JerzySukiennik/gzowo-glass/renders/glass-scan-side.png

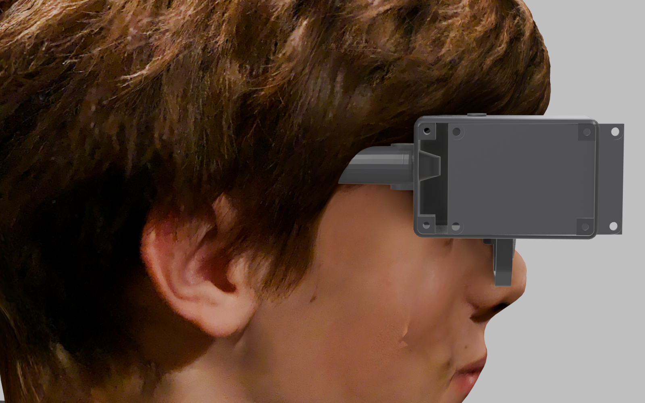
renders/glass-scan-side.png
