JerzySukiennik/gzowo-glass/renders/glass-scan-top-xray.png

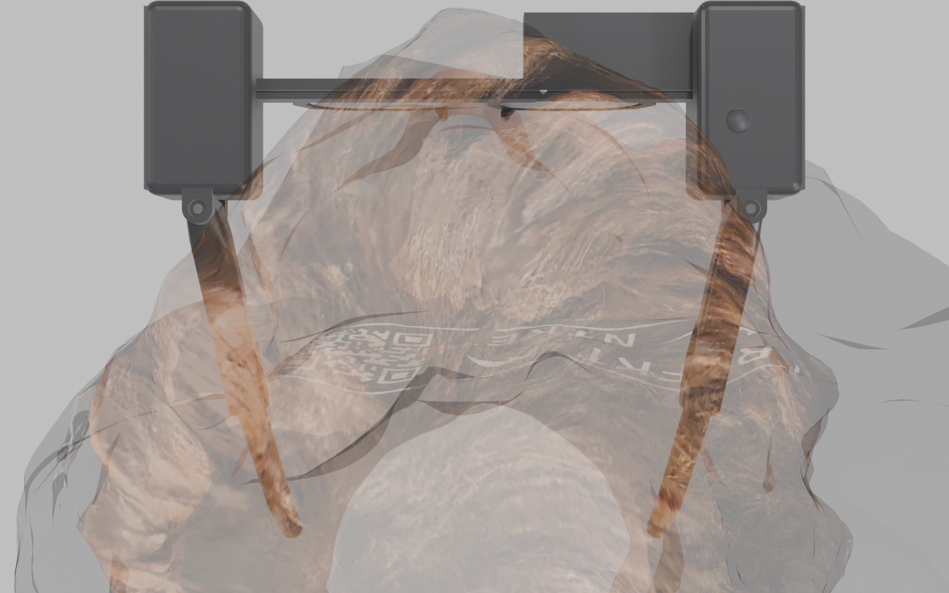
renders/glass-scan-top-xray.png
