JerzySukiennik/gzowo-glass/docs/glass/assets/v0.6/exploded.png

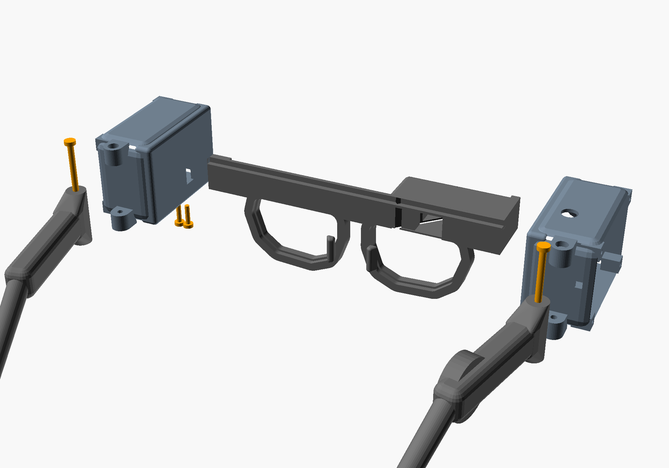
docs/glass/assets/v0.6/exploded.png
