JerzySukiennik/gzowo-glass/docs/glass/assets/v0.6/eye.webp

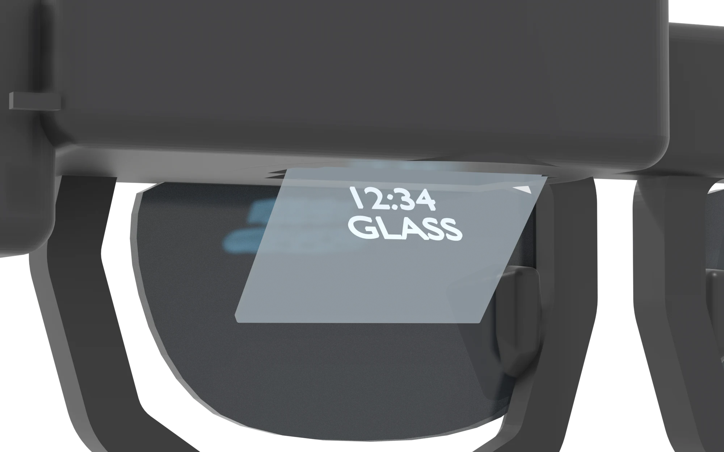
docs/glass/assets/v0.6/eye.webp
