JerzySukiennik/gzowo-glass/docs/glass/assets/v0.6/frames/f036.webp

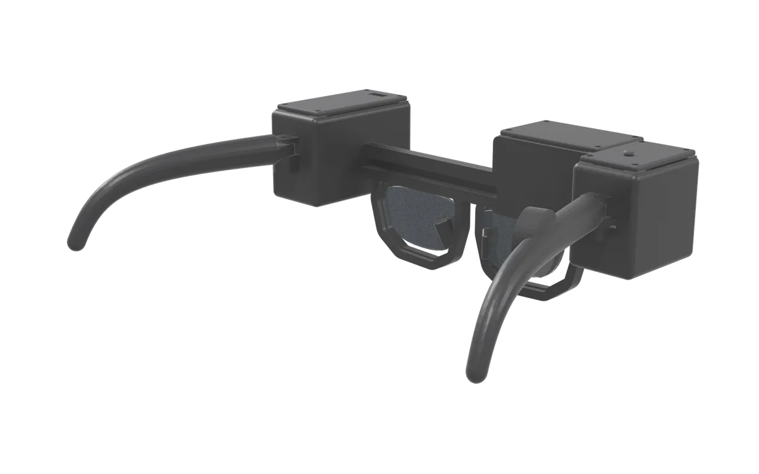
docs/glass/assets/v0.6/frames/f036.webp
