JerzySukiennik/gzowo-glass/docs/glass/assets/v0.6/frames/f054.webp

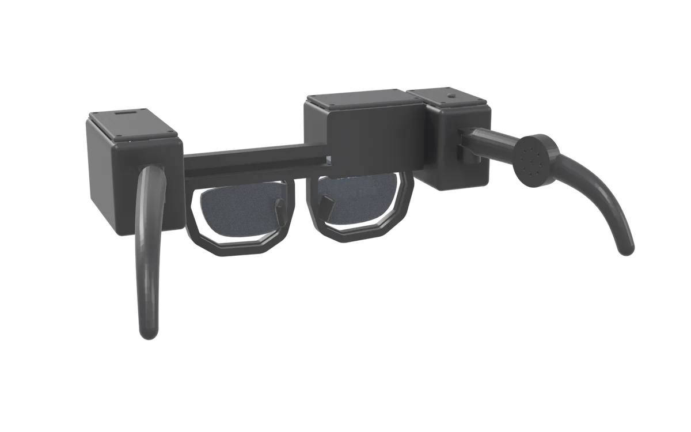
docs/glass/assets/v0.6/frames/f054.webp
