JerzySukiennik/gzowo-glass/docs/glass/assets/v0.6/frames/f074.webp

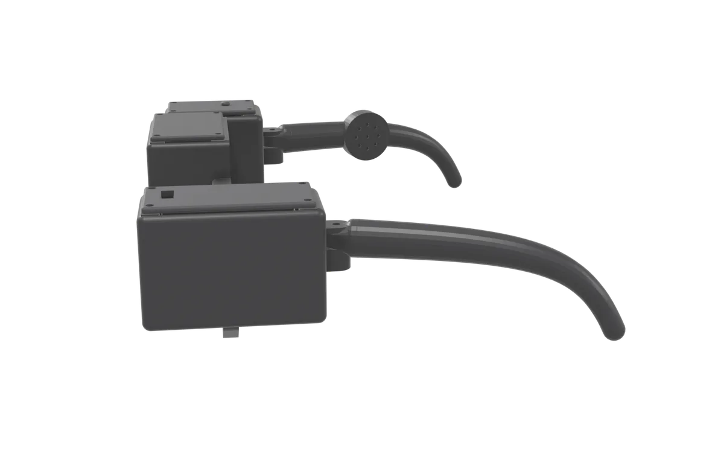
docs/glass/assets/v0.6/frames/f074.webp
