JerzySukiennik/gzowo-glass/docs/glass/assets/v0.6/frames/f085.webp

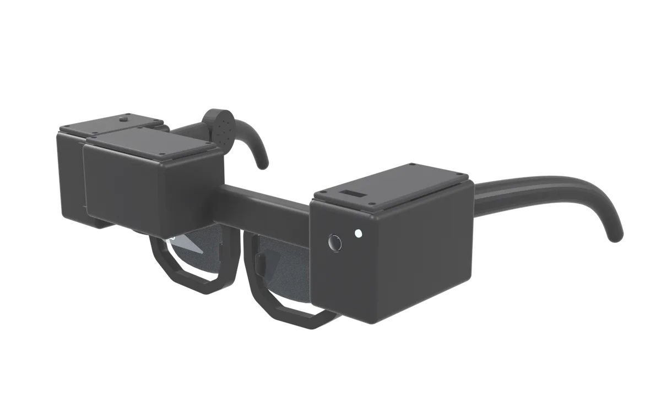
docs/glass/assets/v0.6/frames/f085.webp
