JerzySukiennik/gzowo-glass/docs/glass/assets/v0.6/front.webp

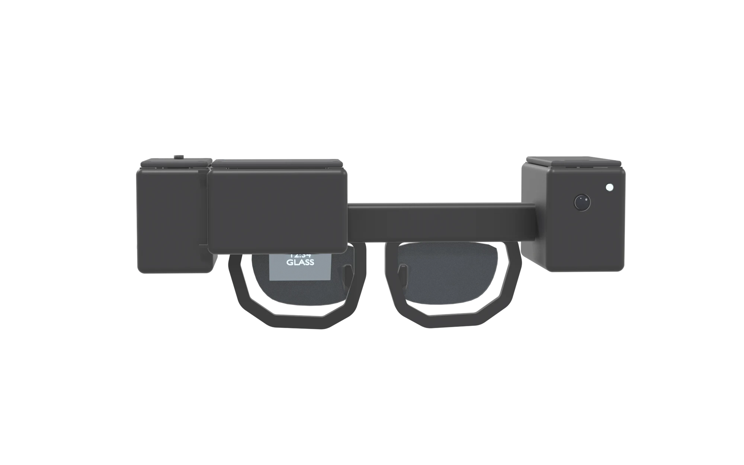
docs/glass/assets/v0.6/front.webp
