JerzySukiennik/gzowo-glass/docs/glass/assets/v0.6/head.webp

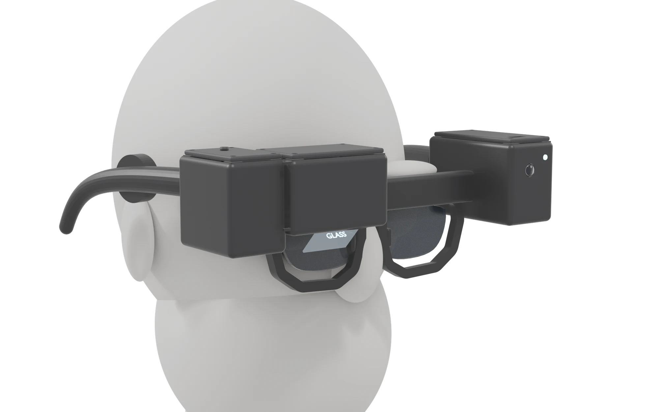
docs/glass/assets/v0.6/head.webp
