JerzySukiennik/gzowo-glass/docs/glass/assets/v0.6/hero.webp

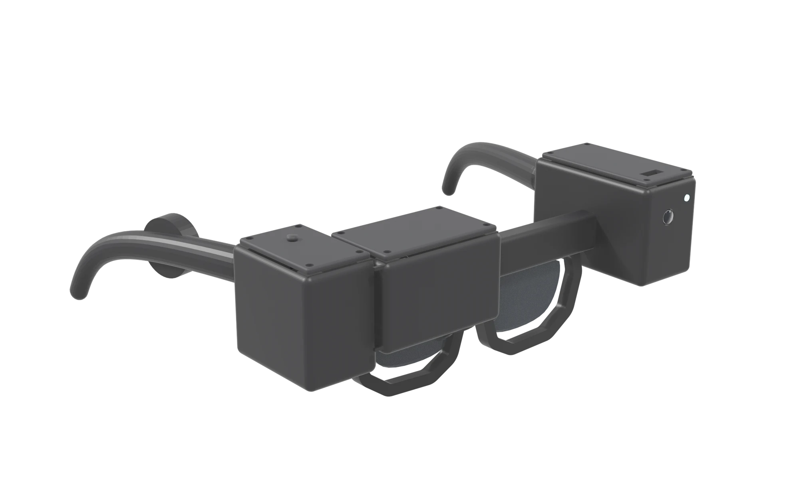
docs/glass/assets/v0.6/hero.webp
