JerzySukiennik/gzowo-glass/docs/glass/assets/v0.6/left.webp

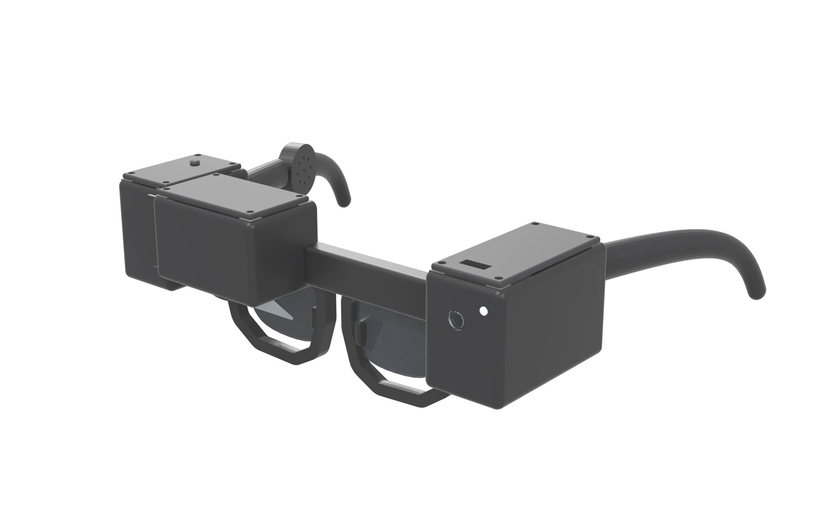
docs/glass/assets/v0.6/left.webp
