JerzySukiennik/gzowo-glass/docs/glass/assets/v0.6/pod.webp

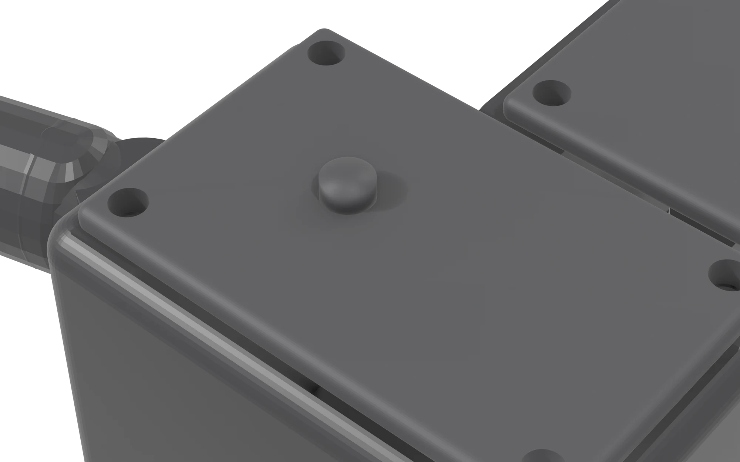
docs/glass/assets/v0.6/pod.webp
