JerzySukiennik/gzowo-glass/docs/smendilendi/assets/v0.5/detail.webp

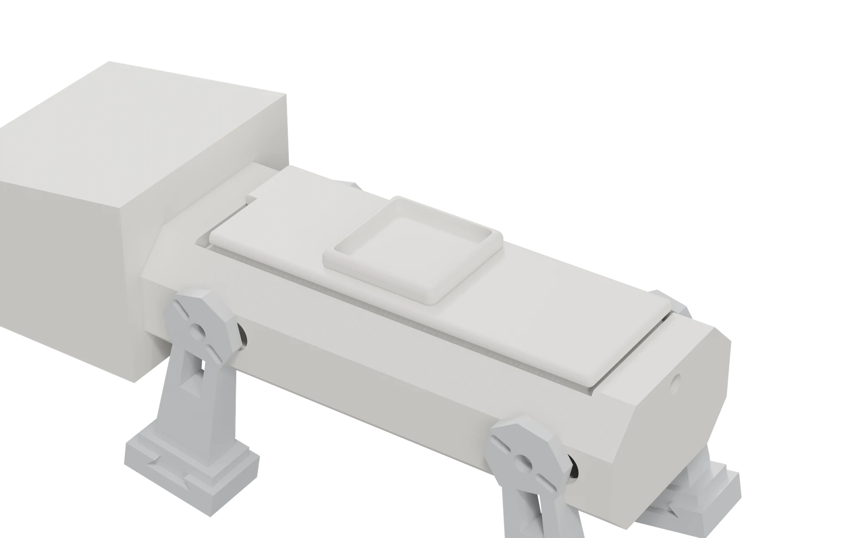
docs/smendilendi/assets/v0.5/detail.webp
