JerzySukiennik/gzowo-glass/docs/smendilendi/assets/v0.5/frames/f015.webp

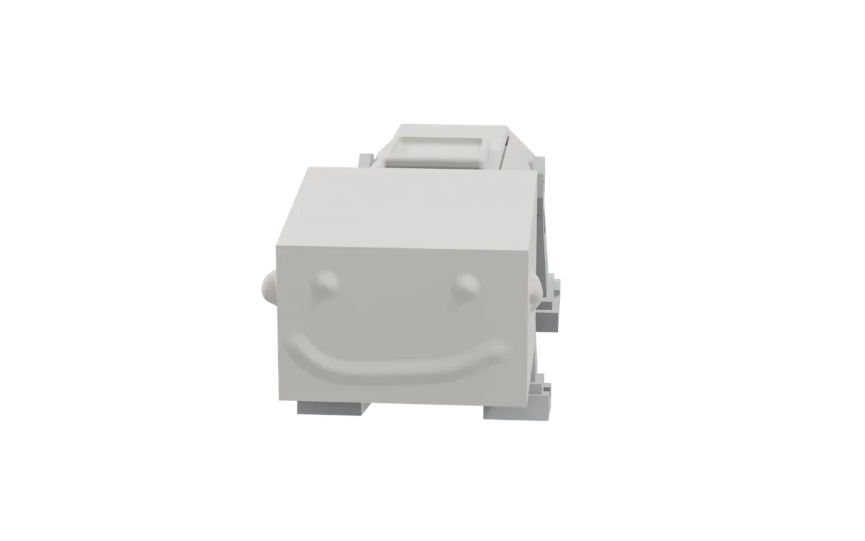
docs/smendilendi/assets/v0.5/frames/f015.webp
