JerzySukiennik/gzowo-glass/docs/smendilendi/assets/v0.5/frames/f086.webp

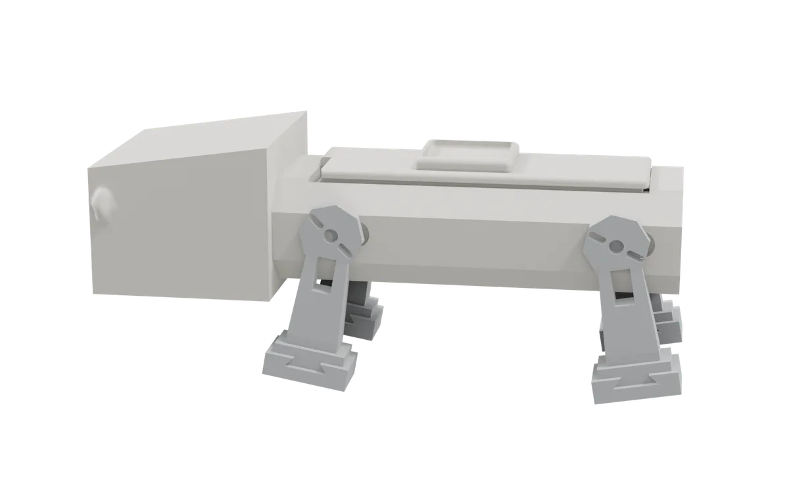
docs/smendilendi/assets/v0.5/frames/f086.webp
