JerzySukiennik/gzowo-glass/docs/smendilendi/assets/v0.5/front.webp

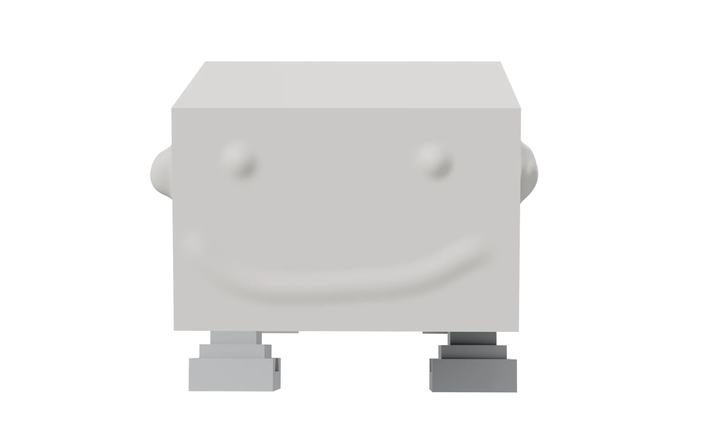
docs/smendilendi/assets/v0.5/front.webp
