JerzySukiennik/gzowo-glass/docs/smendilendi/assets/v0.5/head.webp

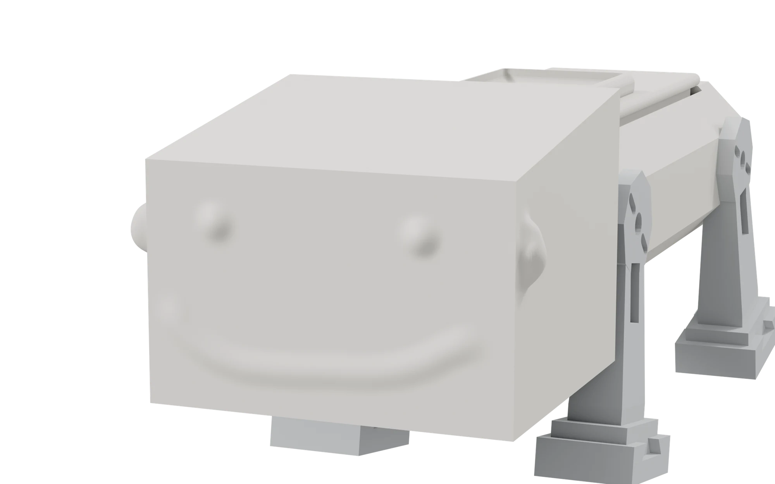
docs/smendilendi/assets/v0.5/head.webp
