JerzySukiennik/gzowo-glass/docs/smendilendi/assets/v0.5/hero.webp

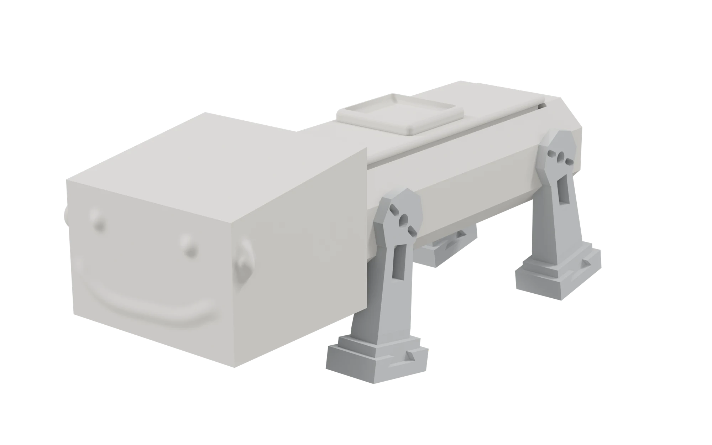
docs/smendilendi/assets/v0.5/hero.webp
