JerzySukiennik/gzowo-glass/docs/smendilendi/assets/v0.5/top.webp

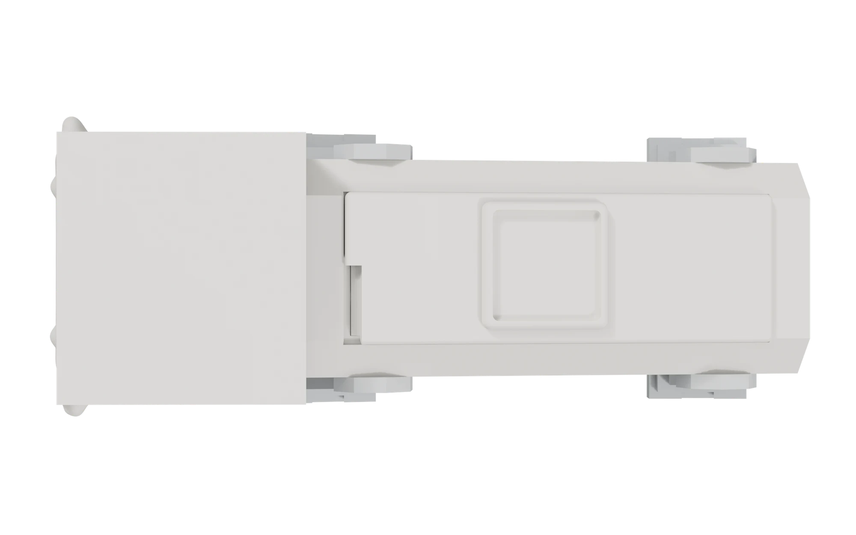
docs/smendilendi/assets/v0.5/top.webp
