JerzySukiennik/gzowo-glass/renders/frames/f000.png

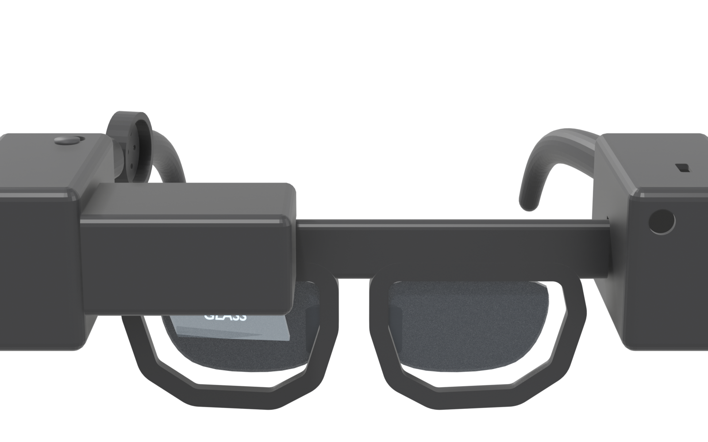
renders/frames/f000.png
