JerzySukiennik/gzowo-glass/renders/frames/f001.png

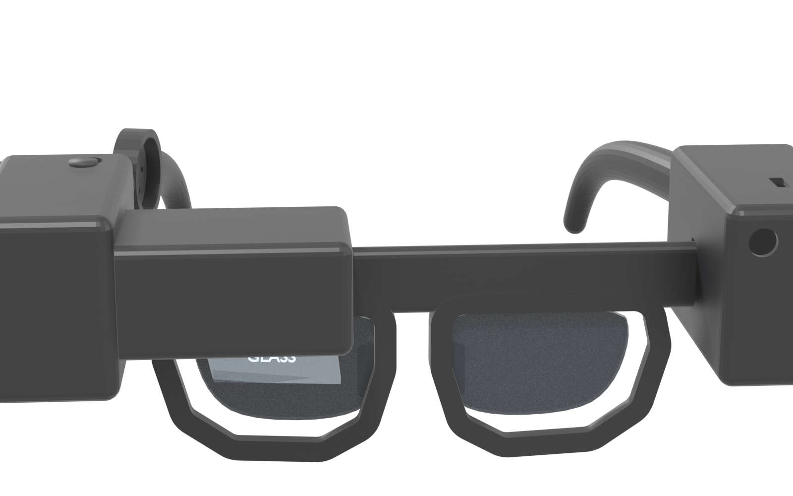
renders/frames/f001.png
