JerzySukiennik/gzowo-glass/renders/frames/f002.png

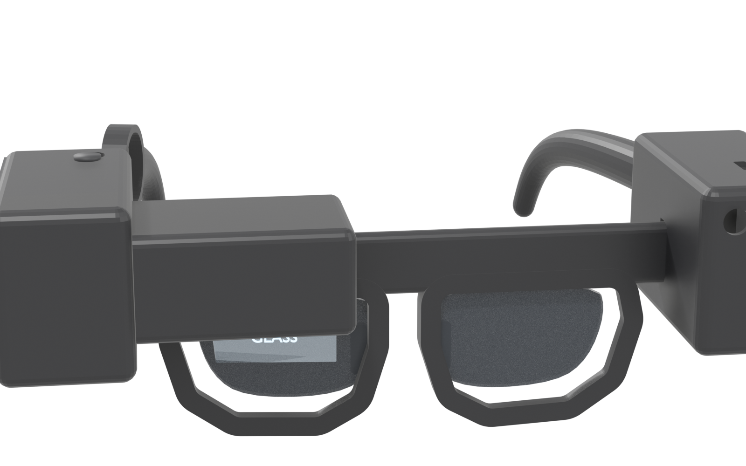
renders/frames/f002.png
