JerzySukiennik/gzowo-glass/renders/frames/f003.png

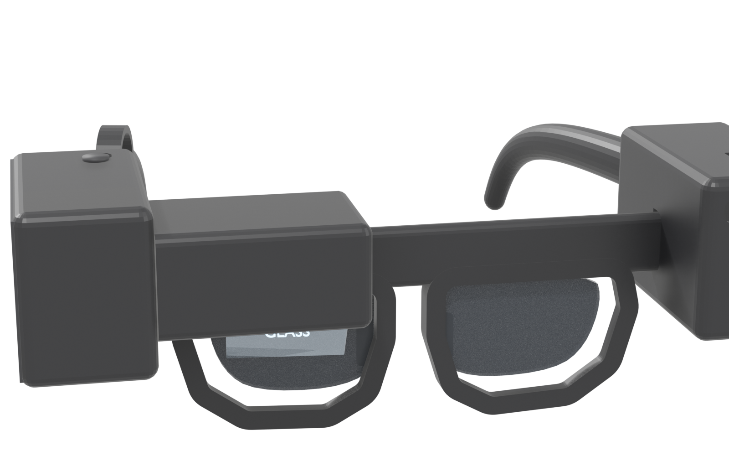
renders/frames/f003.png
