JerzySukiennik/gzowo-glass/renders/frames/f004.png

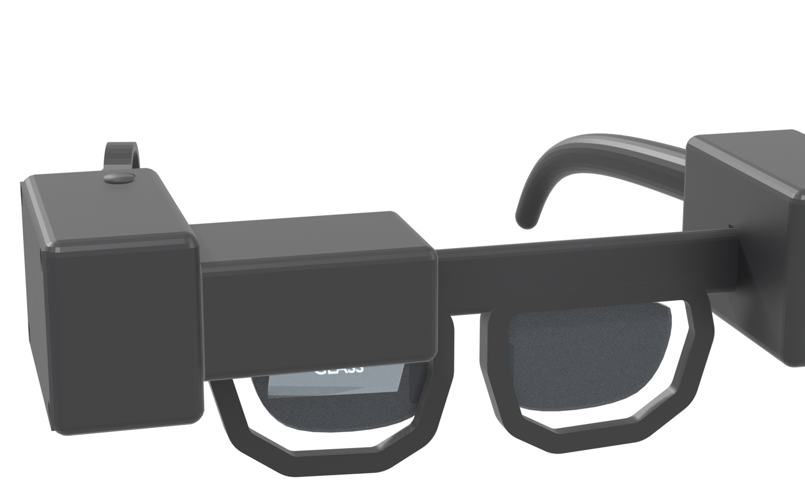
renders/frames/f004.png
