JerzySukiennik/gzowo-glass/renders/frames/f005.png

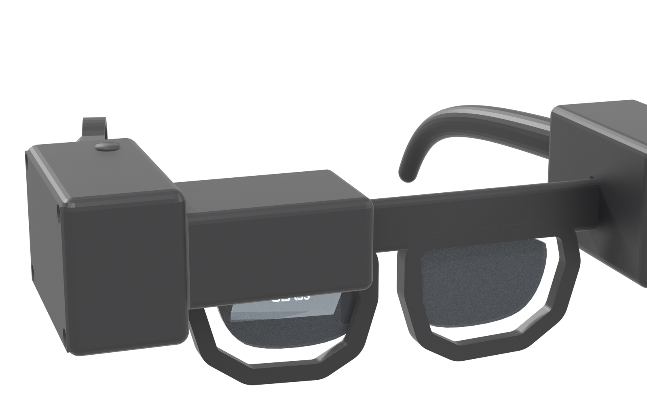
renders/frames/f005.png
