JerzySukiennik/gzowo-glass/renders/frames/f006.png

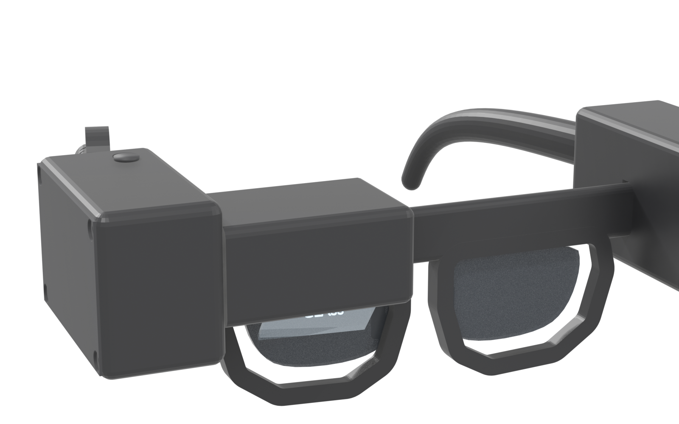
renders/frames/f006.png
