JerzySukiennik/gzowo-glass/renders/frames/f007.png

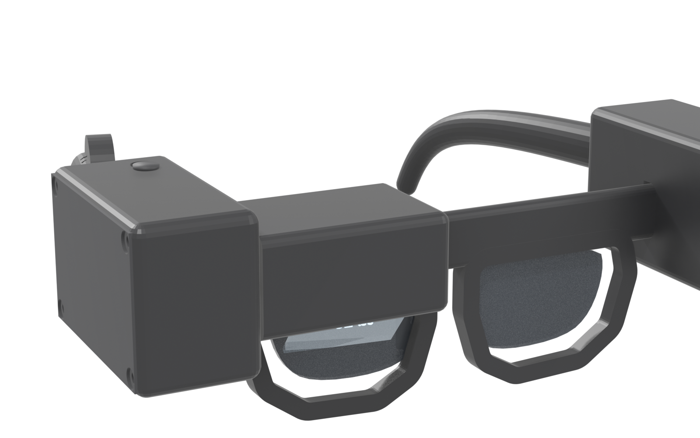
renders/frames/f007.png
