JerzySukiennik/gzowo-glass/renders/frames/f008.png

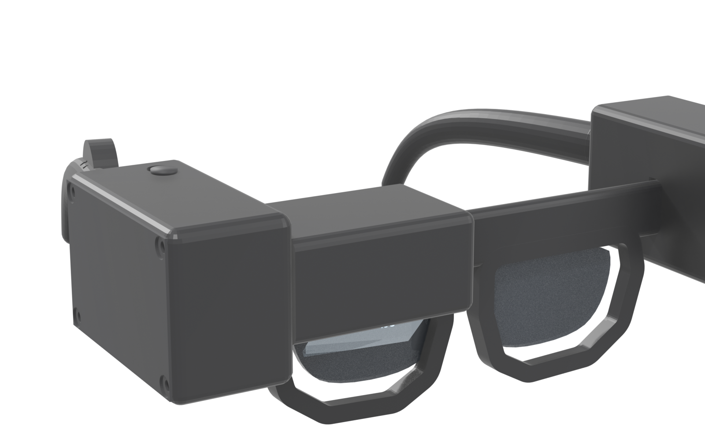
renders/frames/f008.png
