JerzySukiennik/gzowo-glass/renders/frames/f009.png

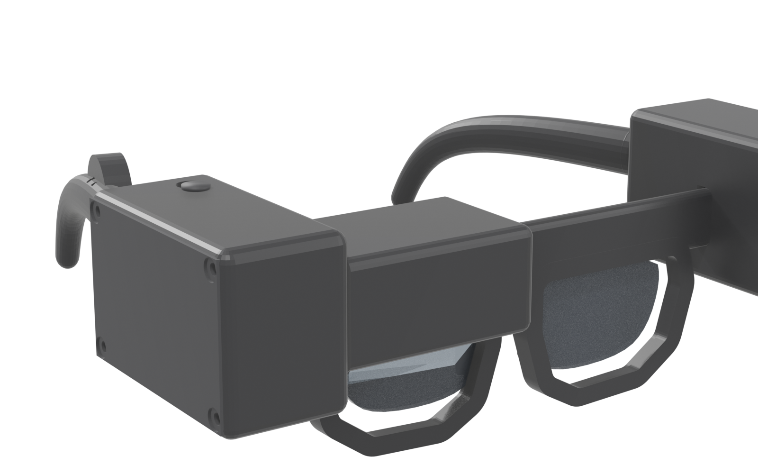
renders/frames/f009.png
