JerzySukiennik/gzowo-glass/renders/frames/f011.png

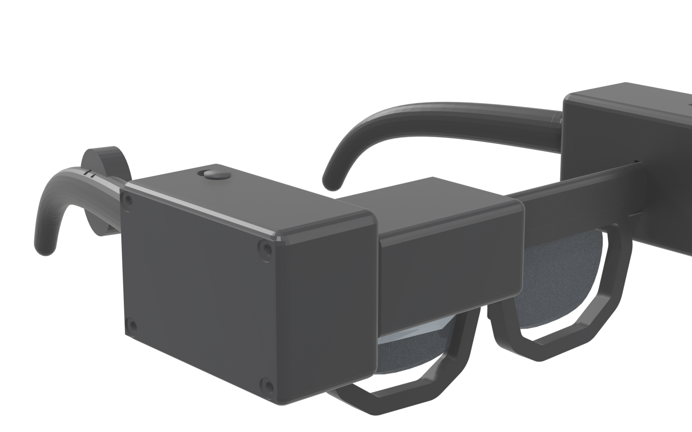
renders/frames/f011.png
