JerzySukiennik/gzowo-glass/renders/frames/f013.png

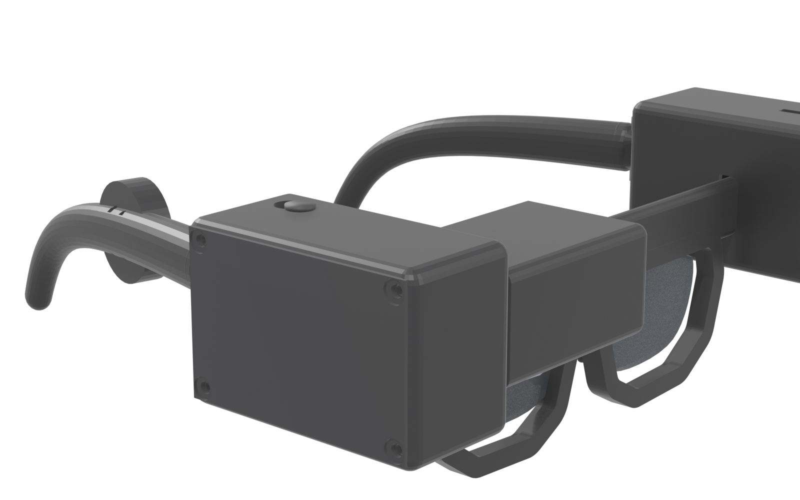
renders/frames/f013.png
