JerzySukiennik/gzowo-glass/renders/frames/f014.png

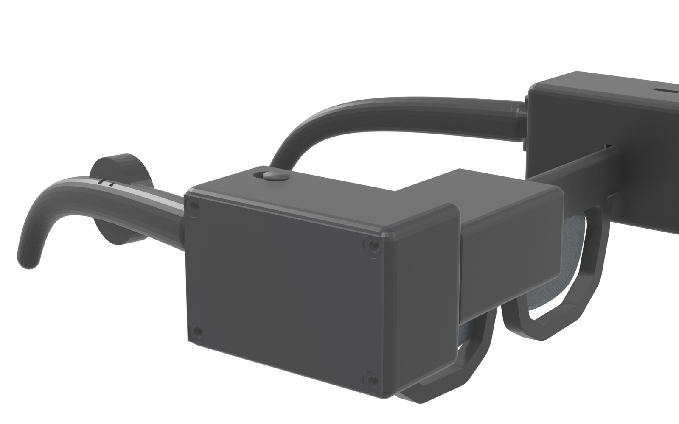
renders/frames/f014.png
