JerzySukiennik/gzowo-glass/renders/frames/f016.png

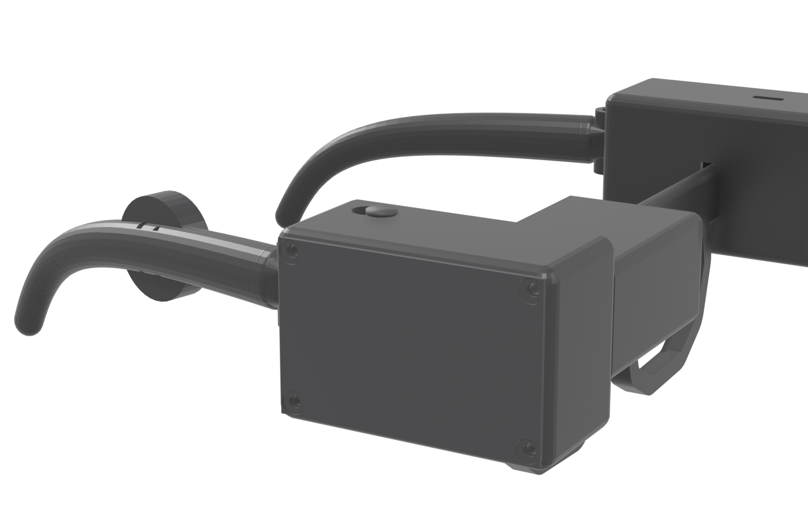
renders/frames/f016.png
