JerzySukiennik/gzowo-glass/renders/frames/f017.png

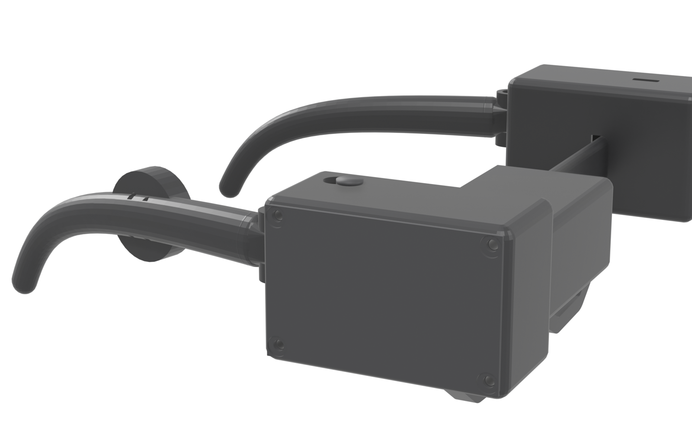
renders/frames/f017.png
