JerzySukiennik/gzowo-glass/renders/frames/f018.png

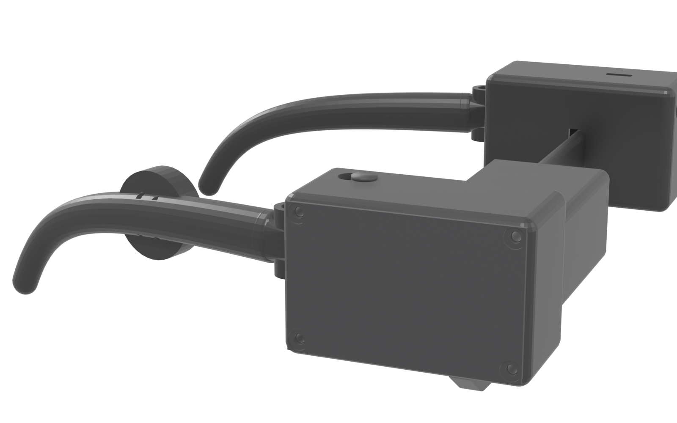
renders/frames/f018.png
