JerzySukiennik/gzowo-glass/renders/frames/f020.png

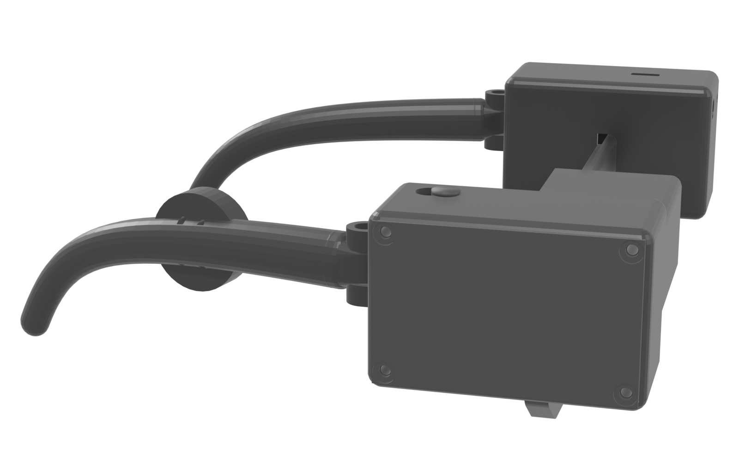
renders/frames/f020.png
