JerzySukiennik/gzowo-glass/renders/frames/f023.png

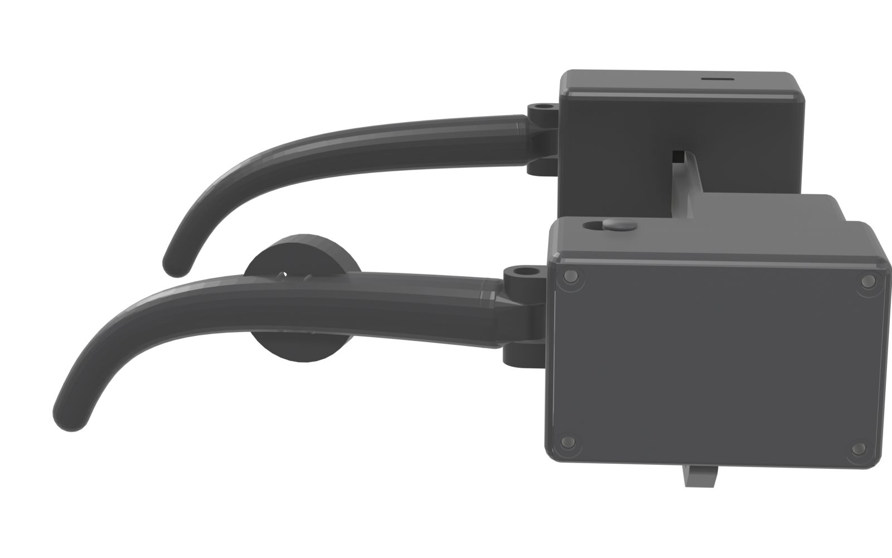
renders/frames/f023.png
