JerzySukiennik/gzowo-glass/renders/frames/f024.png

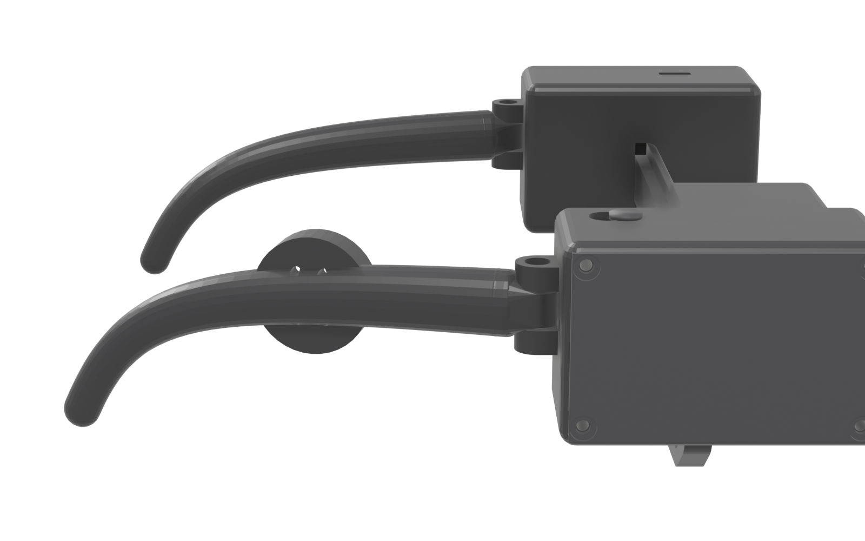
renders/frames/f024.png
