JerzySukiennik/gzowo-glass/renders/frames/f025.png

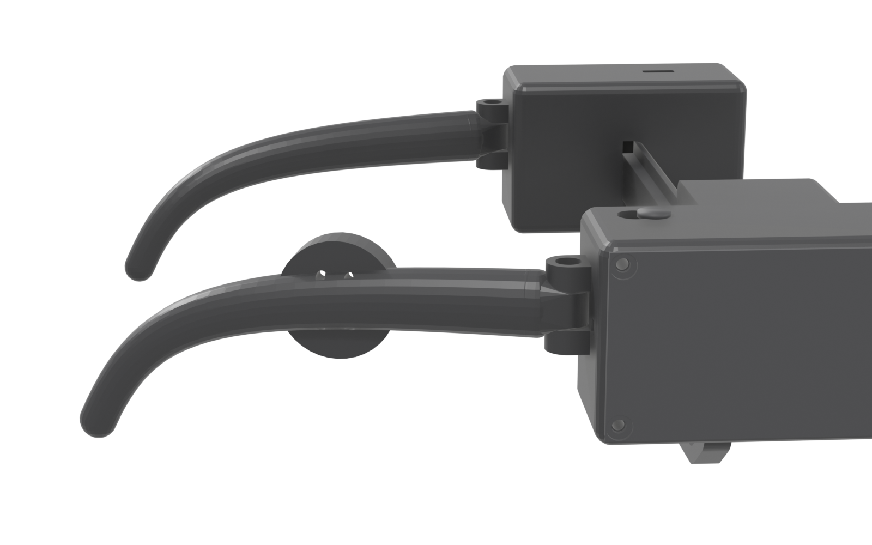
renders/frames/f025.png
