JerzySukiennik/gzowo-glass/renders/frames/f027.png

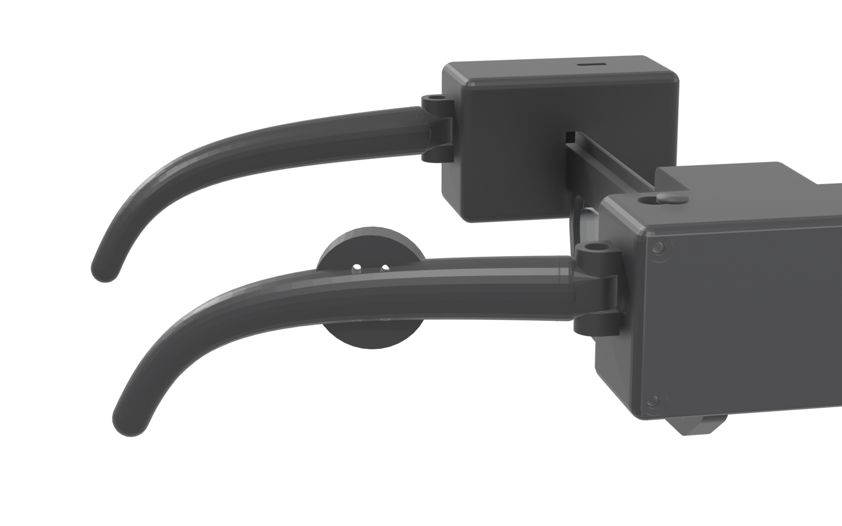
renders/frames/f027.png
