JerzySukiennik/gzowo-glass/renders/frames/f028.png

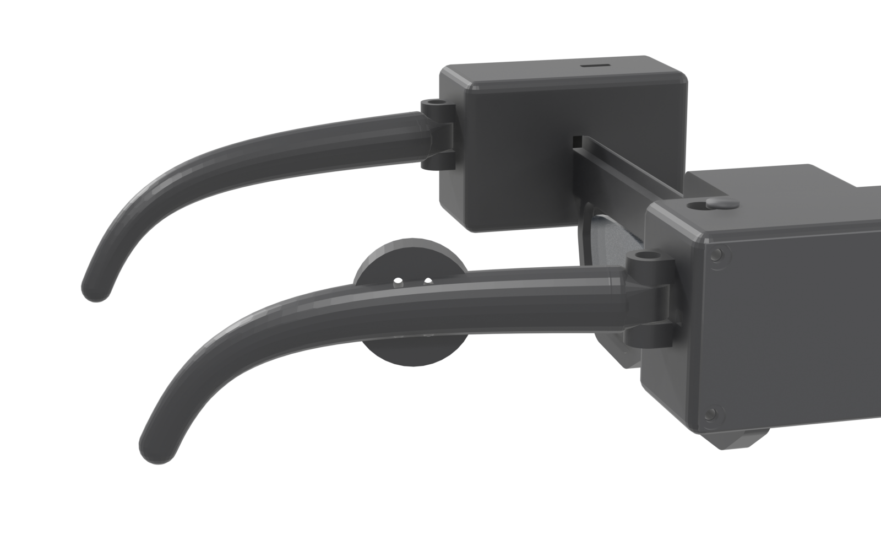
renders/frames/f028.png
