JerzySukiennik/gzowo-glass/renders/frames/f030.png

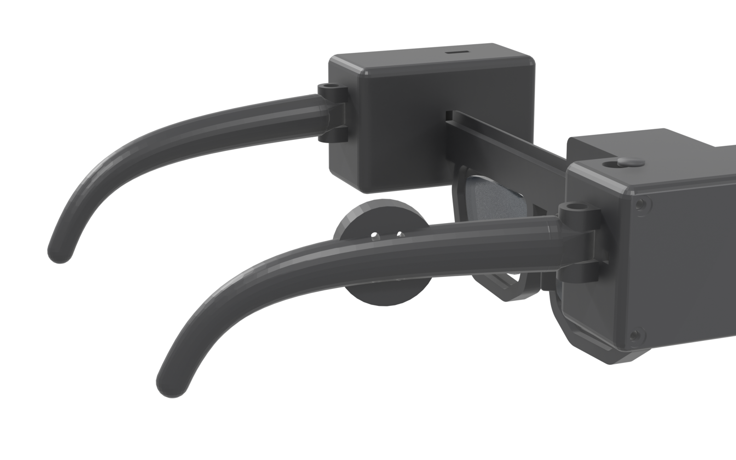
renders/frames/f030.png
