JerzySukiennik/gzowo-glass/renders/frames/f032.png

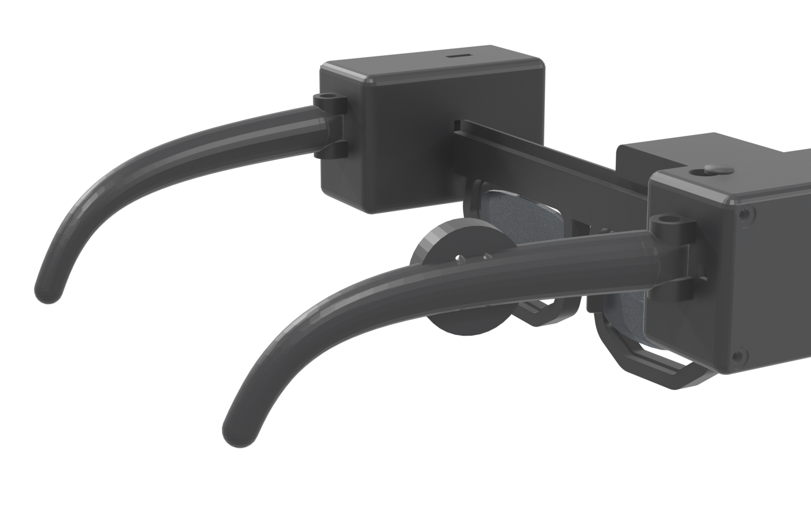
renders/frames/f032.png
