JerzySukiennik/gzowo-glass/renders/frames/f033.png

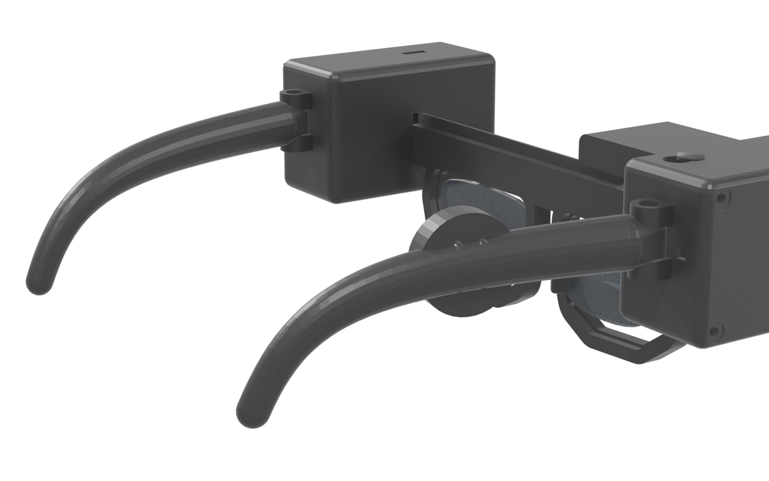
renders/frames/f033.png
