JerzySukiennik/gzowo-glass/renders/frames/f034.png

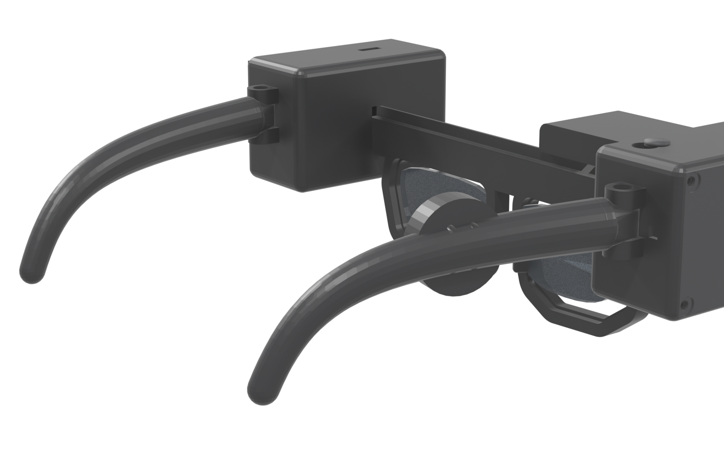
renders/frames/f034.png
