JerzySukiennik/gzowo-glass/renders/frames/f035.png

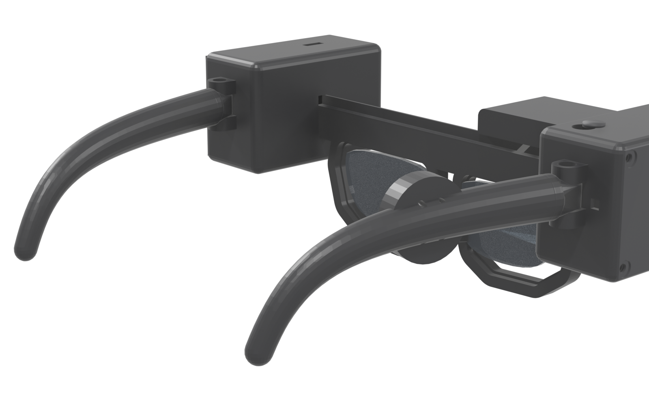
renders/frames/f035.png
