JerzySukiennik/gzowo-glass/renders/frames/f037.png

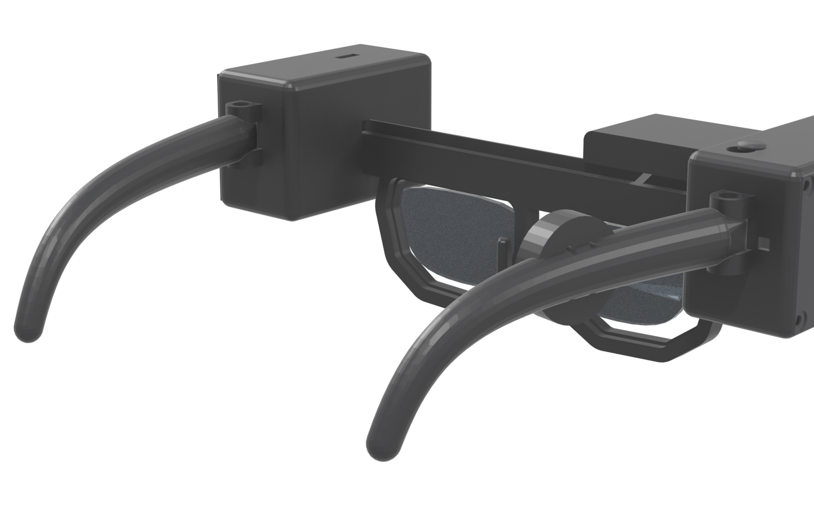
renders/frames/f037.png
