JerzySukiennik/gzowo-glass/renders/frames/f039.png

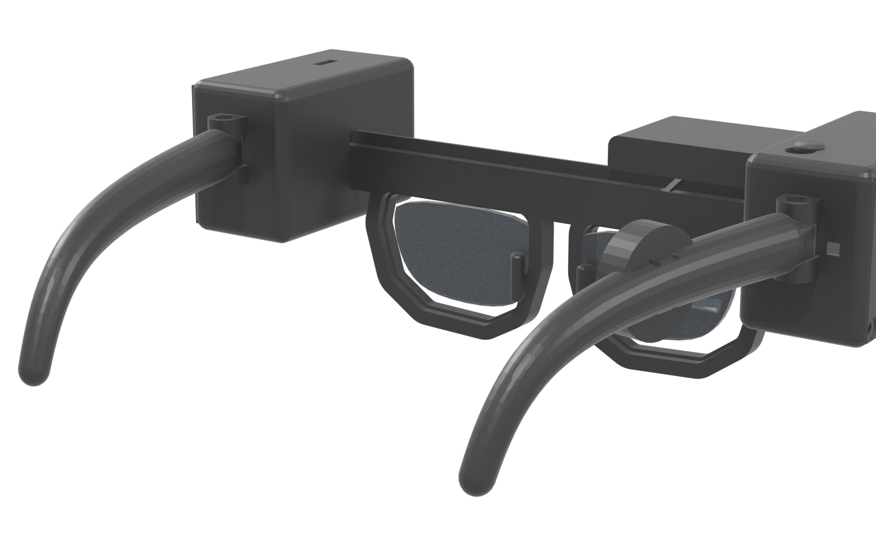
renders/frames/f039.png
