JerzySukiennik/gzowo-glass/renders/frames/f040.png

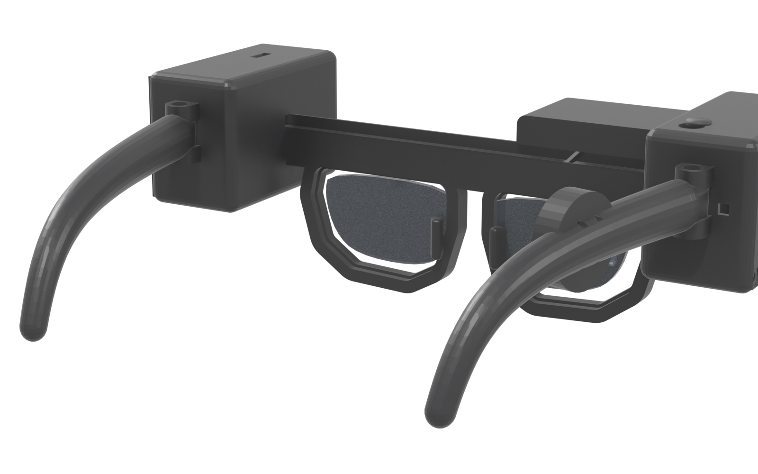
renders/frames/f040.png
