JerzySukiennik/gzowo-glass/renders/frames/f041.png

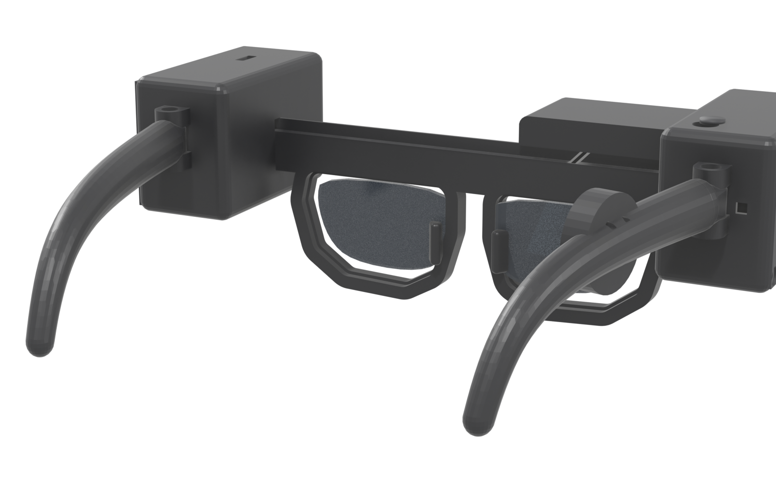
renders/frames/f041.png
