JerzySukiennik/gzowo-glass/renders/frames/f042.png

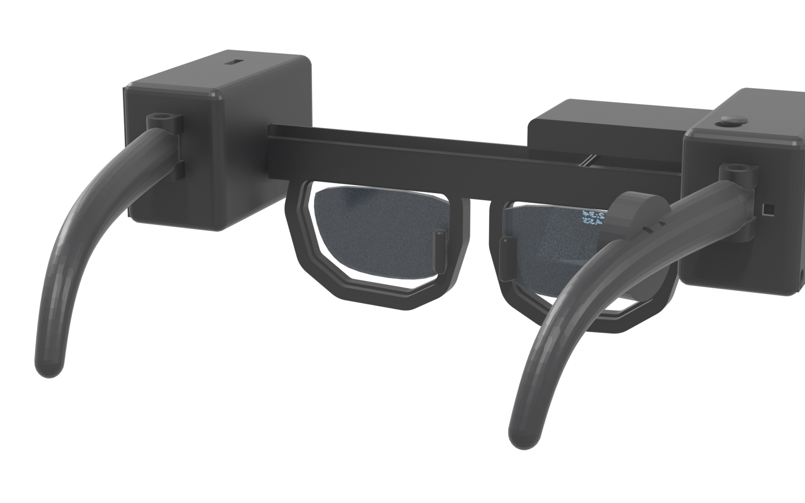
renders/frames/f042.png
