JerzySukiennik/gzowo-glass/renders/frames/f043.png

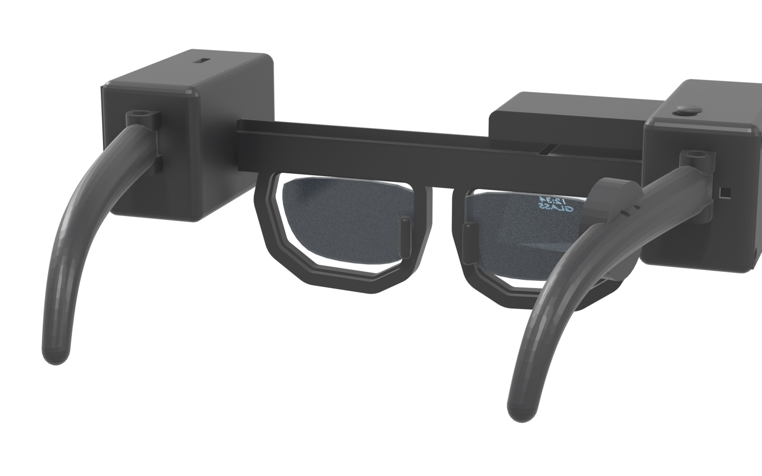
renders/frames/f043.png
