JerzySukiennik/gzowo-glass/renders/frames/f044.png

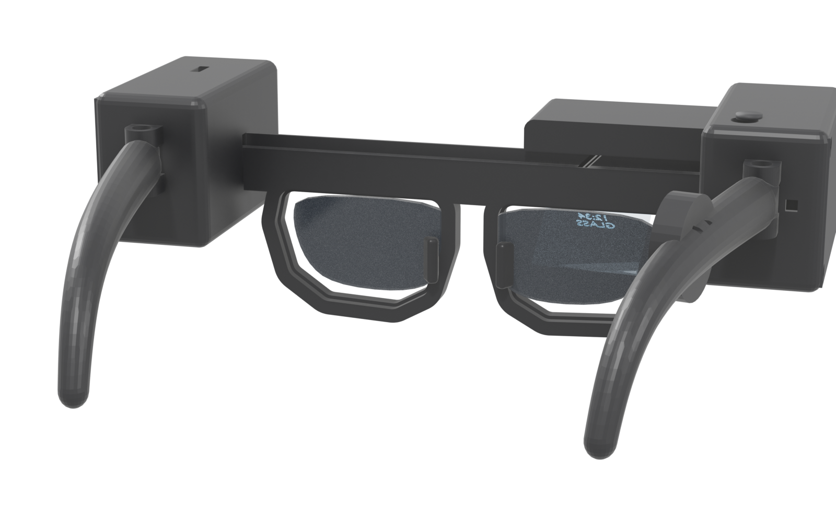
renders/frames/f044.png
