JerzySukiennik/gzowo-glass/renders/frames/f045.png

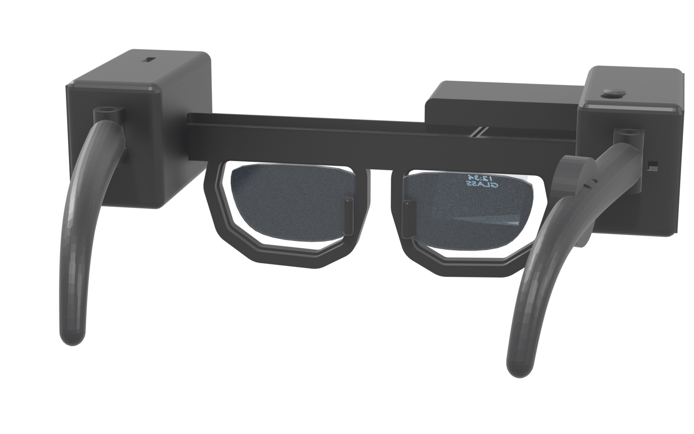
renders/frames/f045.png
