JerzySukiennik/gzowo-glass/renders/frames/f046.png

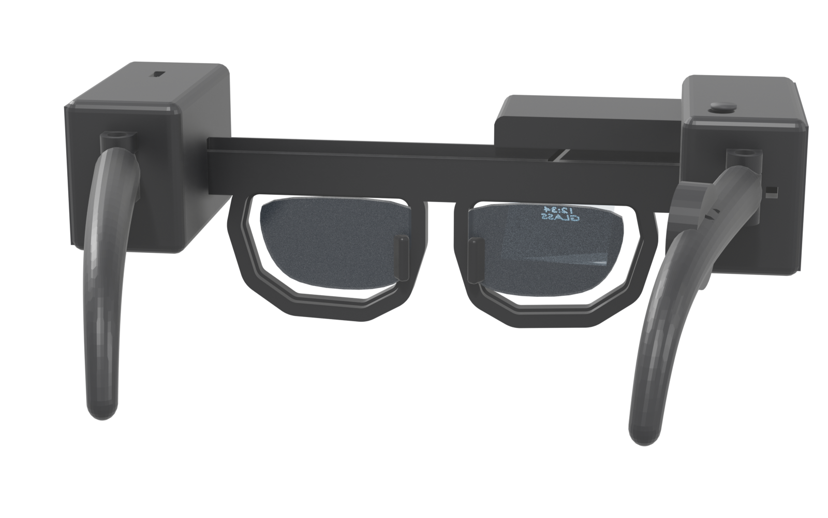
renders/frames/f046.png
