JerzySukiennik/gzowo-glass/renders/frames/f048.png

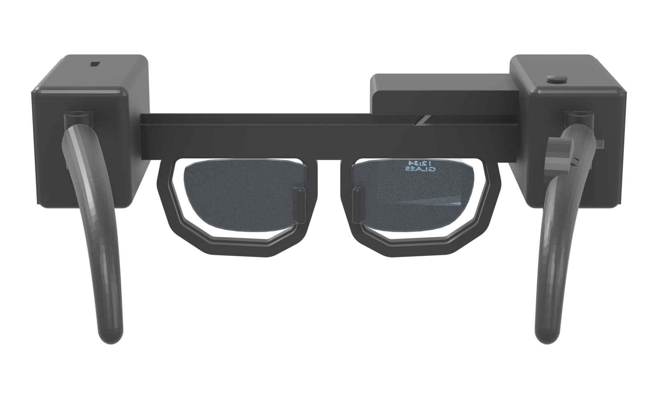
renders/frames/f048.png
