JerzySukiennik/gzowo-glass/renders/frames/f049.png

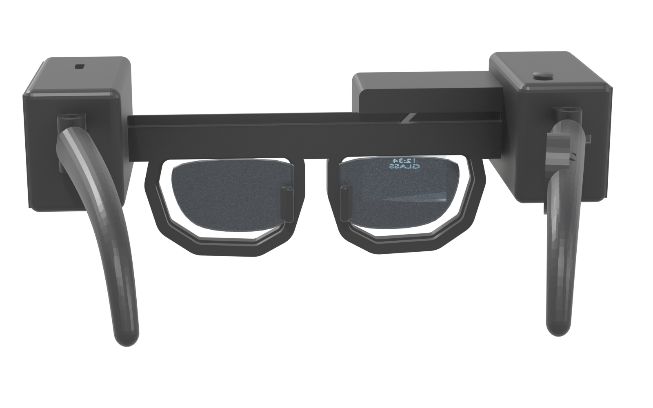
renders/frames/f049.png
