JerzySukiennik/gzowo-glass/renders/frames/f050.png

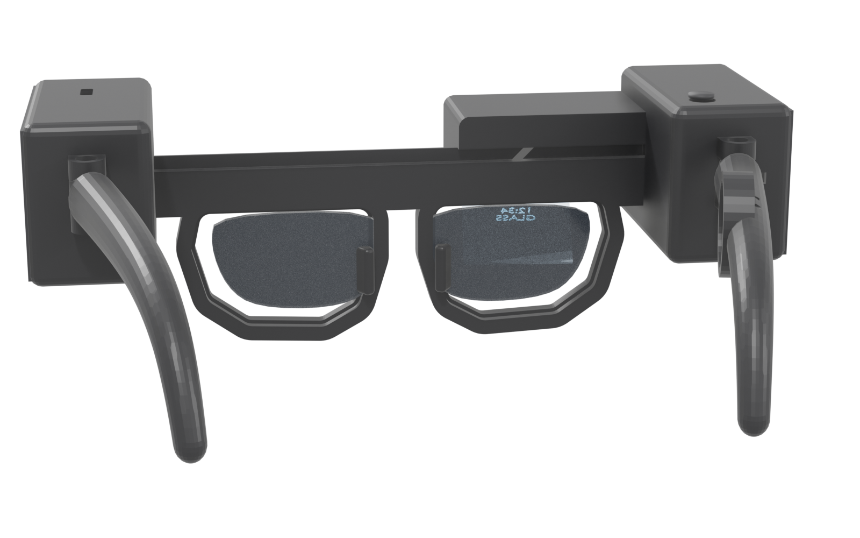
renders/frames/f050.png
