JerzySukiennik/gzowo-glass/renders/frames/f051.png

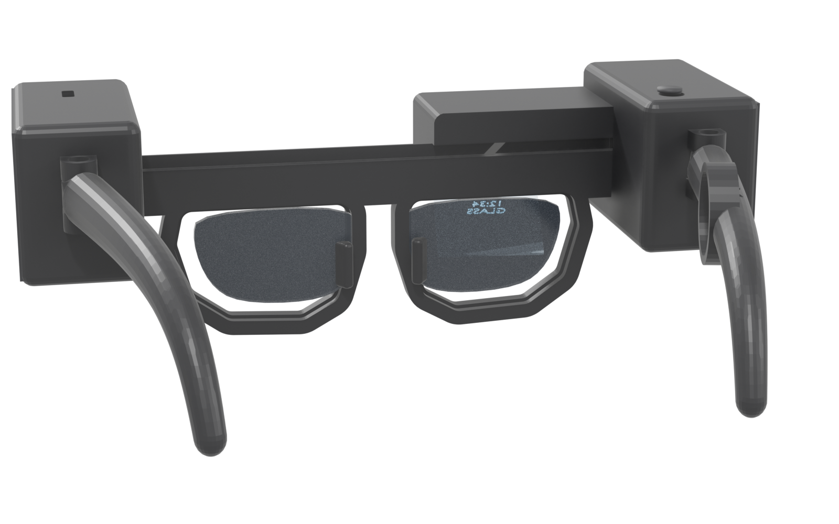
renders/frames/f051.png
