JerzySukiennik/gzowo-glass/renders/frames/f052.png

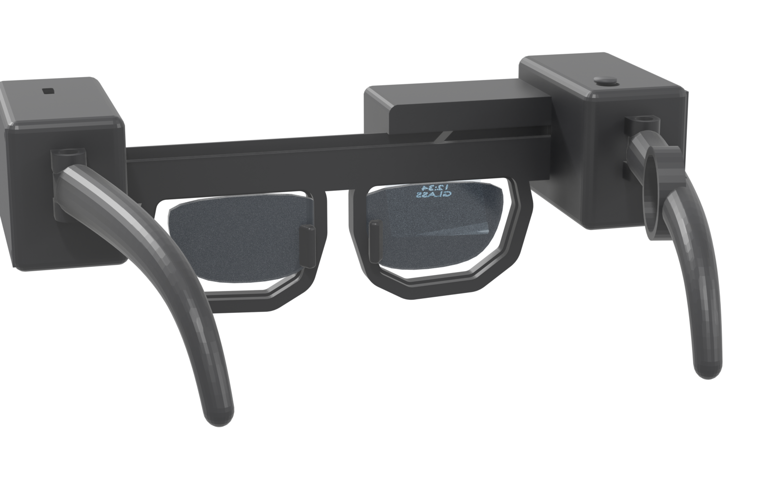
renders/frames/f052.png
