JerzySukiennik/gzowo-glass/renders/frames/f054.png

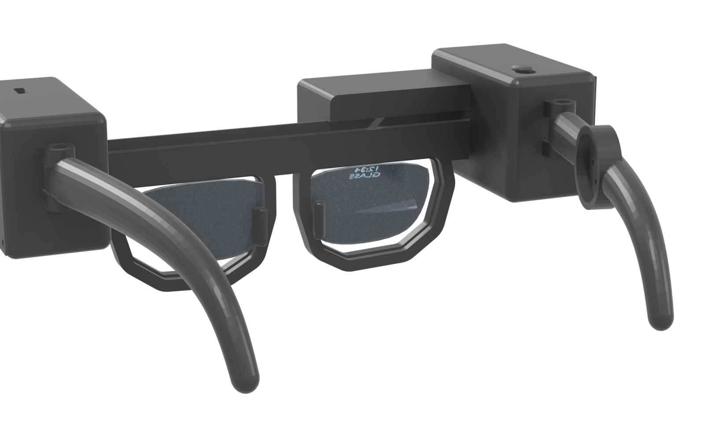
renders/frames/f054.png
