JerzySukiennik/gzowo-glass/renders/frames/f056.png

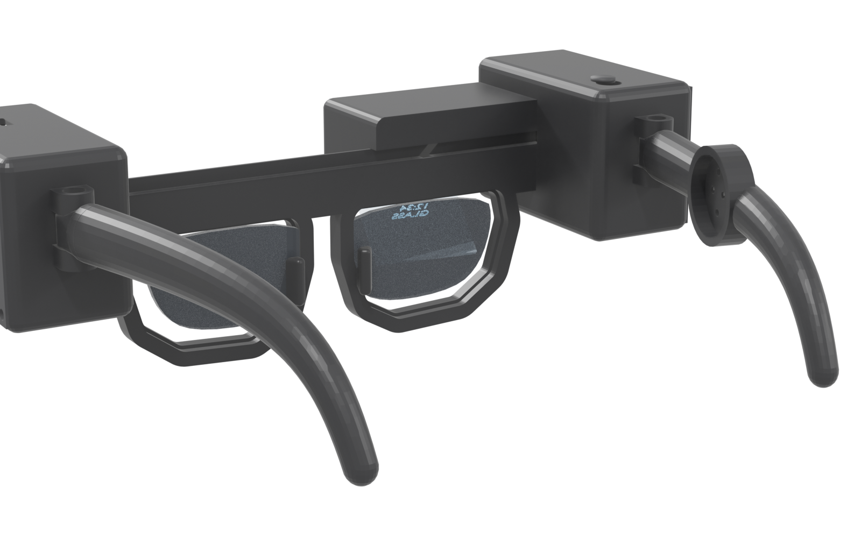
renders/frames/f056.png
