JerzySukiennik/gzowo-glass/renders/frames/f057.png

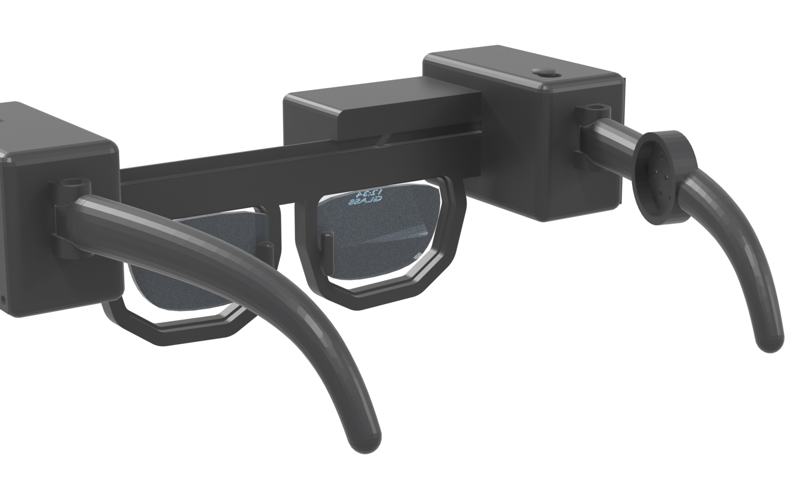
renders/frames/f057.png
