JerzySukiennik/gzowo-glass/renders/frames/f058.png

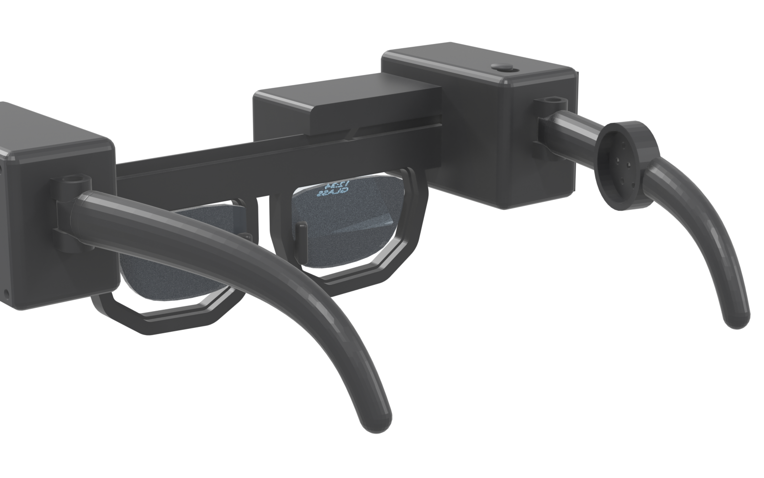
renders/frames/f058.png
