JerzySukiennik/gzowo-glass/renders/frames/f059.png

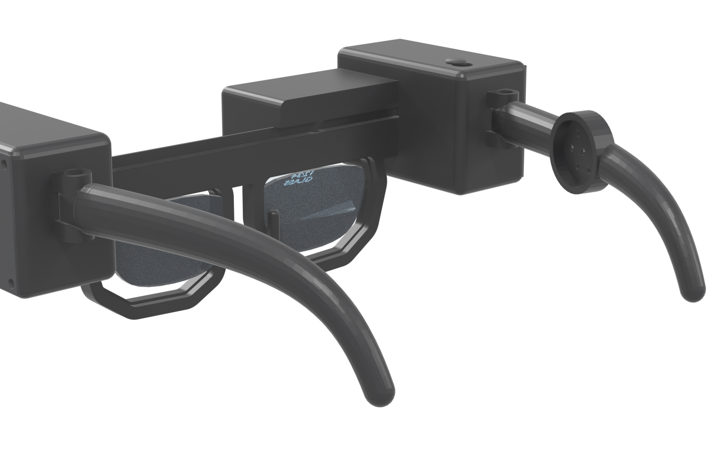
renders/frames/f059.png
