JerzySukiennik/gzowo-glass/renders/frames/f062.png

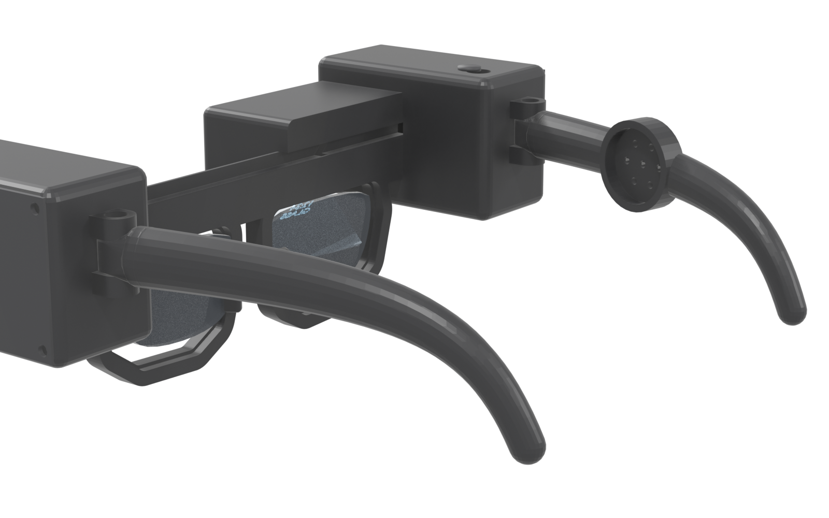
renders/frames/f062.png
