JerzySukiennik/gzowo-glass/renders/frames/f063.png

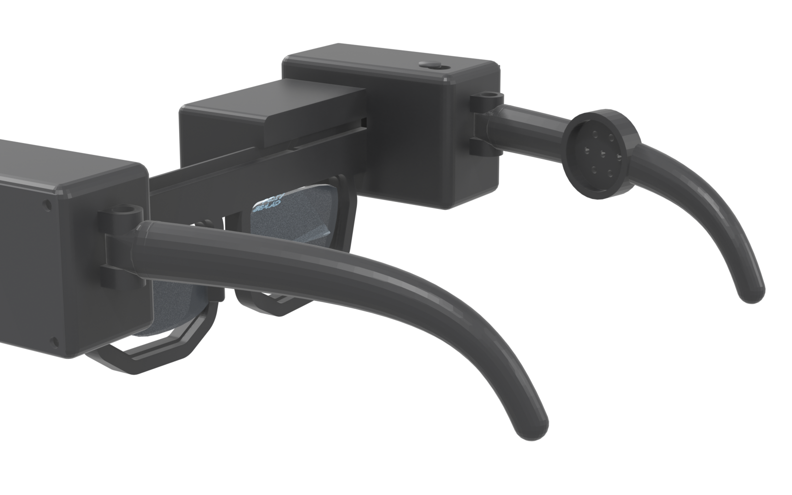
renders/frames/f063.png
