JerzySukiennik/gzowo-glass/renders/frames/f064.png

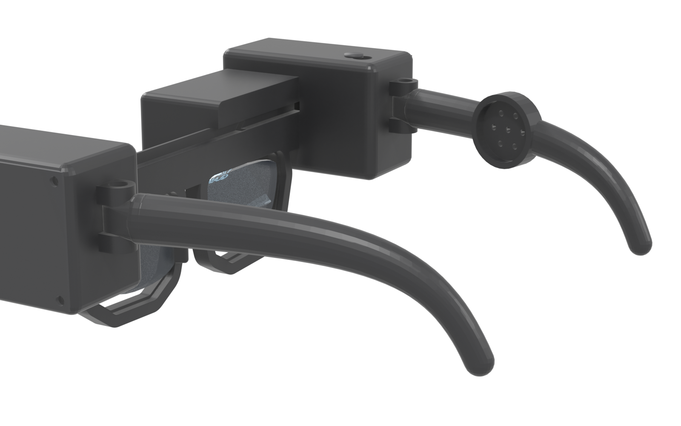
renders/frames/f064.png
