JerzySukiennik/gzowo-glass/renders/frames/f065.png

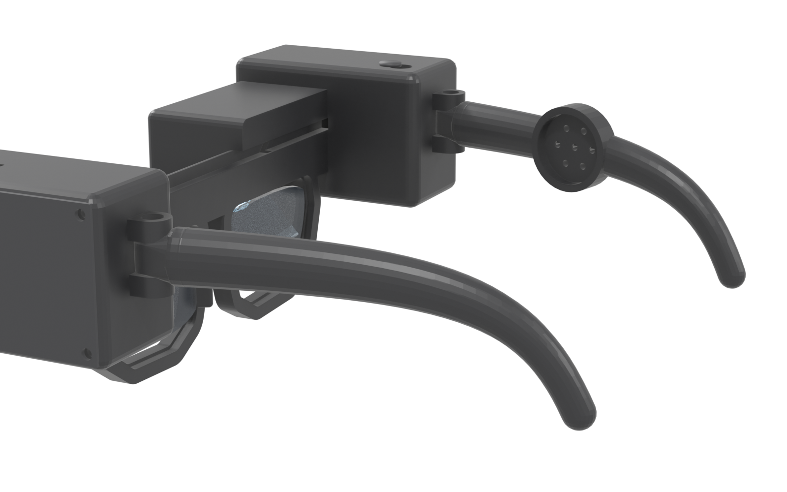
renders/frames/f065.png
