JerzySukiennik/gzowo-glass/renders/frames/f066.png

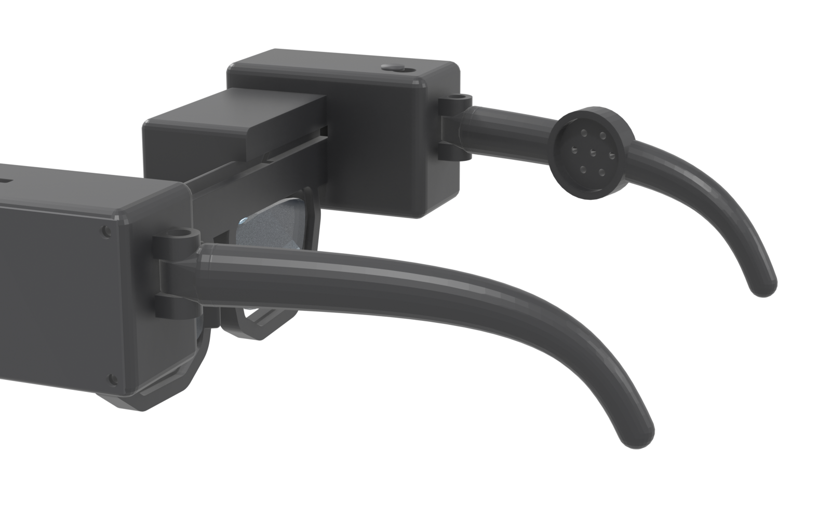
renders/frames/f066.png
