JerzySukiennik/gzowo-glass/renders/frames/f068.png

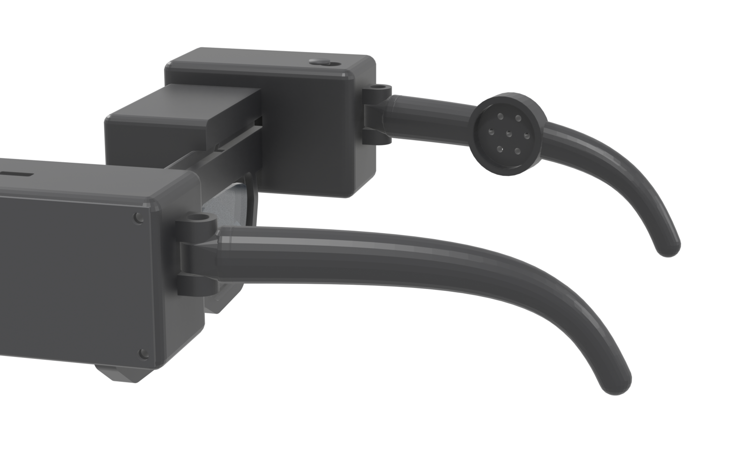
renders/frames/f068.png
