JerzySukiennik/gzowo-glass/renders/frames/f069.png

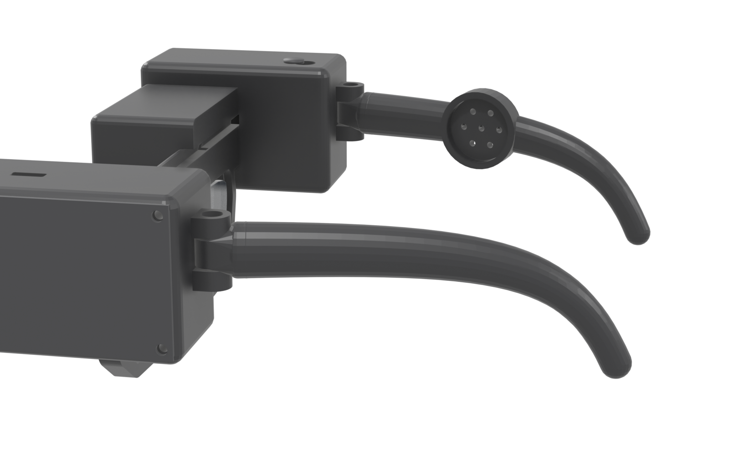
renders/frames/f069.png
