JerzySukiennik/gzowo-glass/renders/frames/f070.png

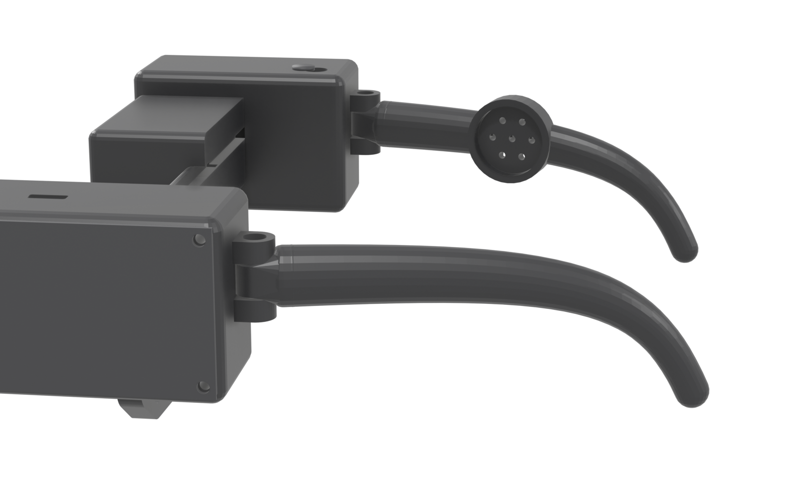
renders/frames/f070.png
