JerzySukiennik/gzowo-glass/renders/frames/f071.png

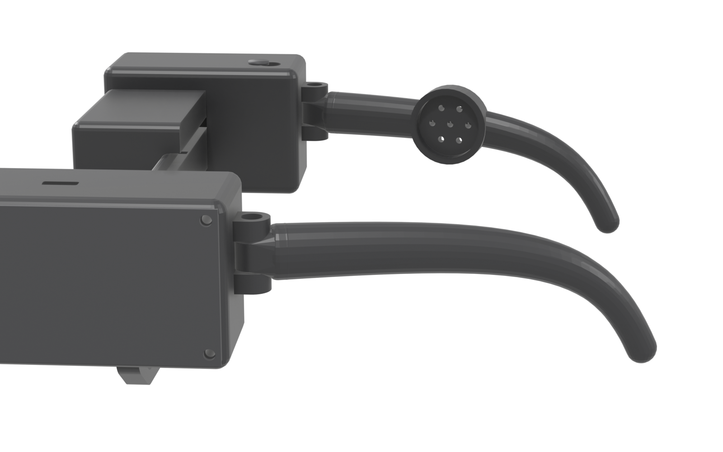
renders/frames/f071.png
