JerzySukiennik/gzowo-glass/renders/frames/f072.png

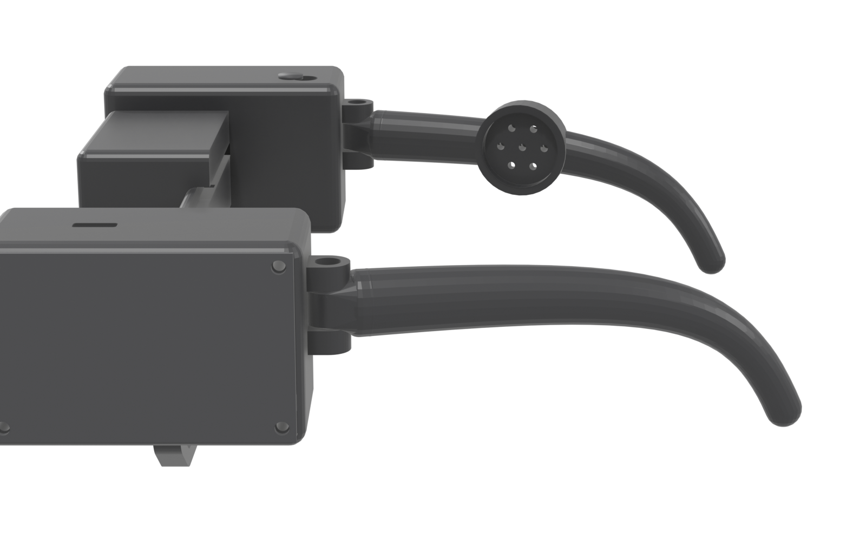
renders/frames/f072.png
