JerzySukiennik/gzowo-glass/renders/frames/f073.png

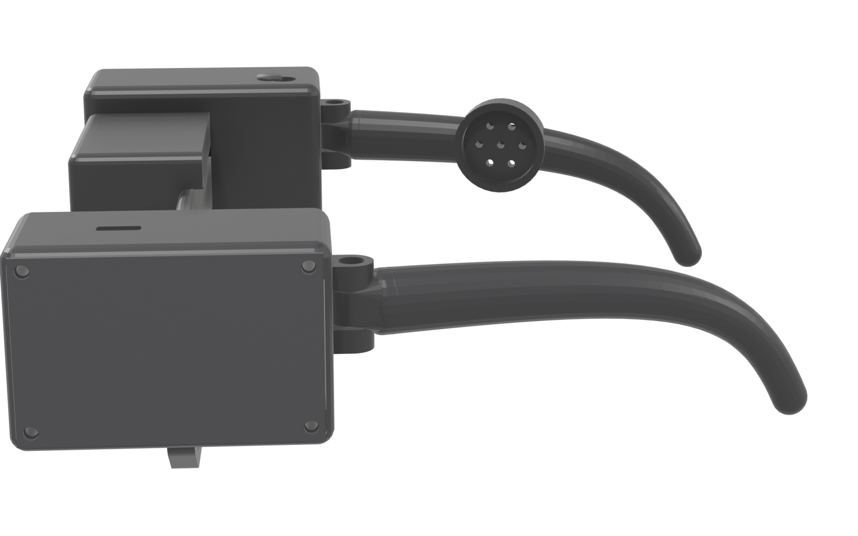
renders/frames/f073.png
