JerzySukiennik/gzowo-glass/renders/frames/f074.png

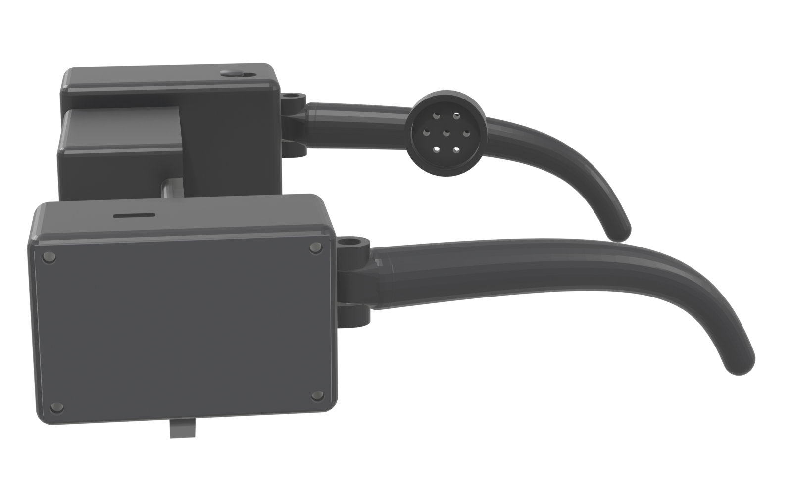
renders/frames/f074.png
