JerzySukiennik/gzowo-glass/renders/frames/f075.png

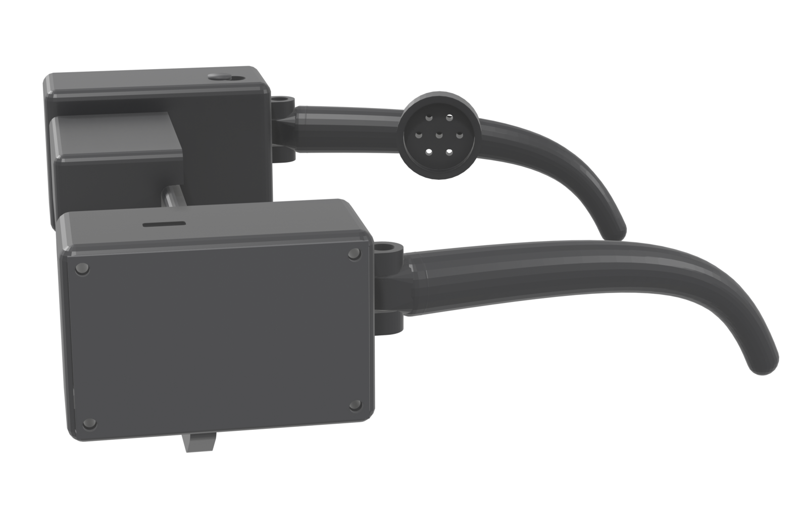
renders/frames/f075.png
