JerzySukiennik/gzowo-glass/renders/frames/f076.png

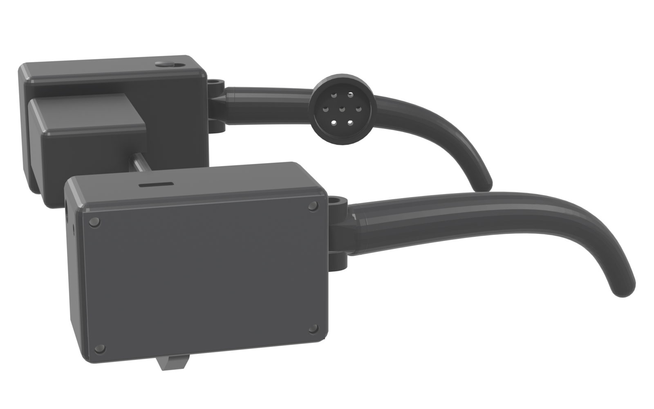
renders/frames/f076.png
