JerzySukiennik/gzowo-glass/renders/frames/f078.png

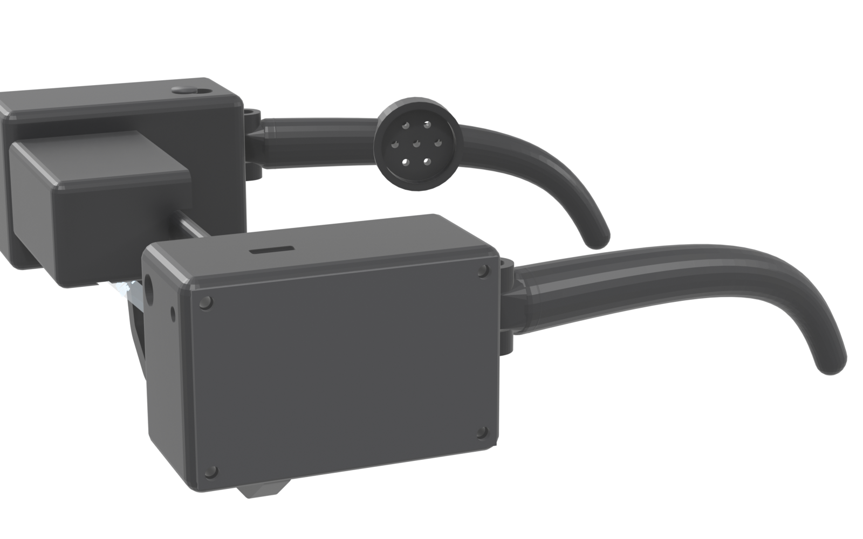
renders/frames/f078.png
