JerzySukiennik/gzowo-glass/renders/frames/f079.png

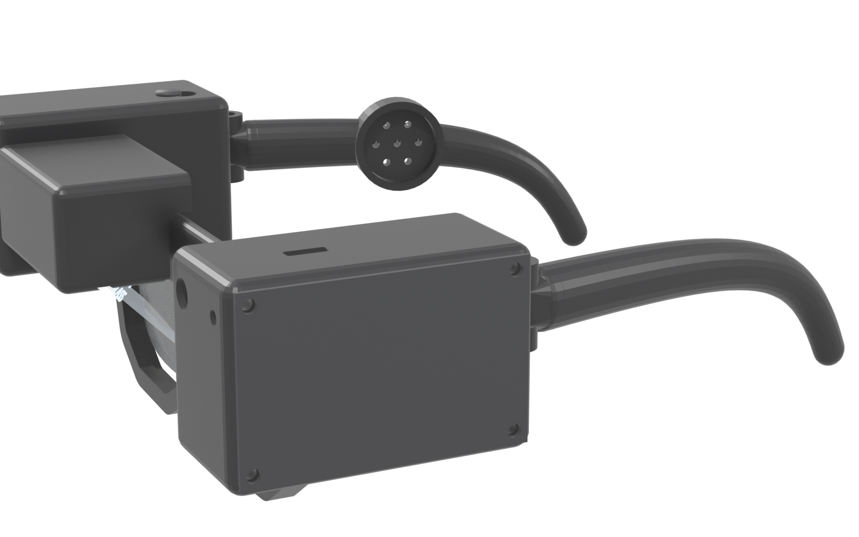
renders/frames/f079.png
