JerzySukiennik/gzowo-glass/renders/frames/f080.png

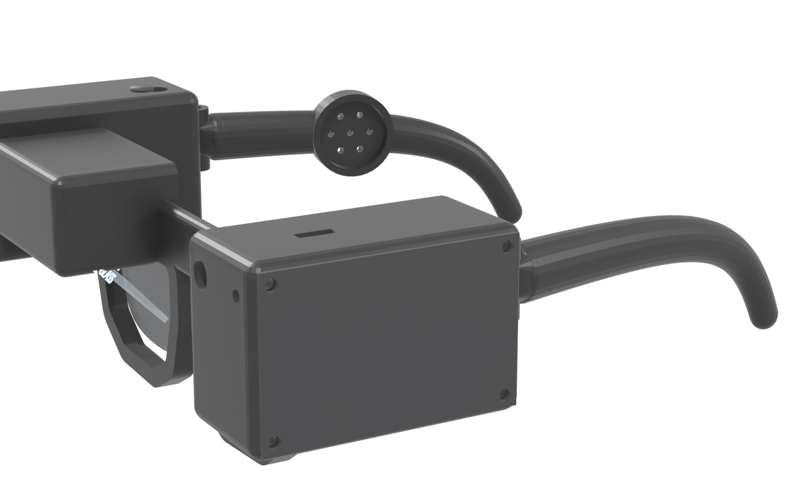
renders/frames/f080.png
