JerzySukiennik/gzowo-glass/renders/frames/f083.png

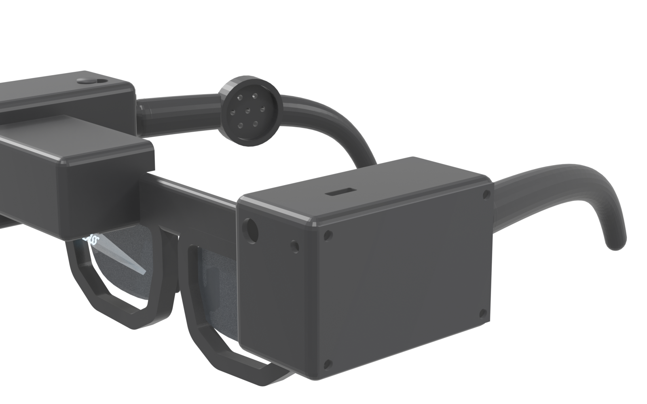
renders/frames/f083.png
