JerzySukiennik/gzowo-glass/renders/frames/f084.png

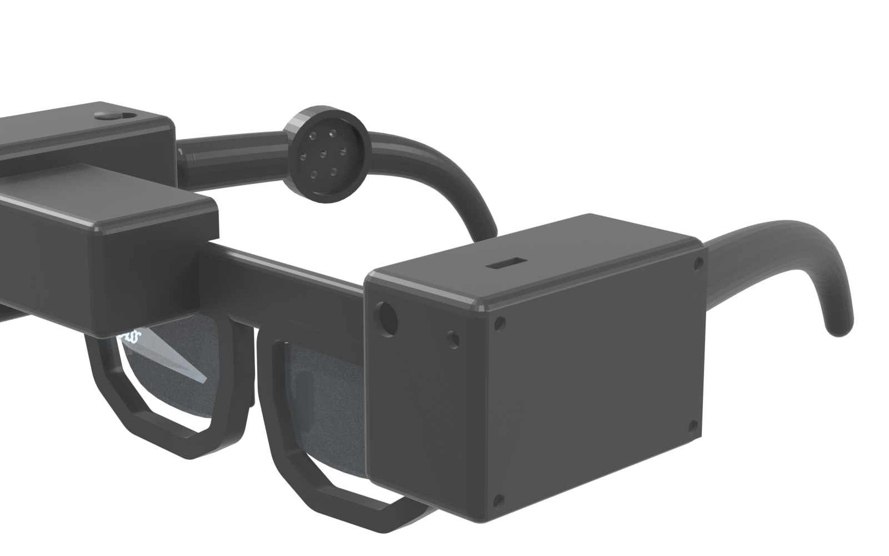
renders/frames/f084.png
