JerzySukiennik/gzowo-glass/renders/frames/f085.png

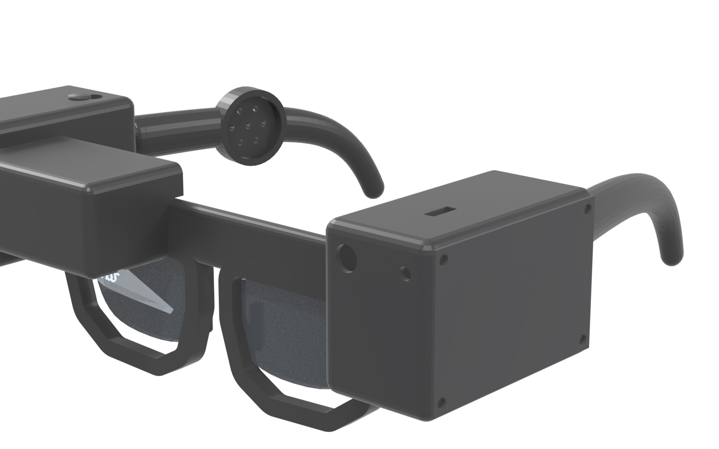
renders/frames/f085.png
