JerzySukiennik/gzowo-glass/renders/frames/f086.png

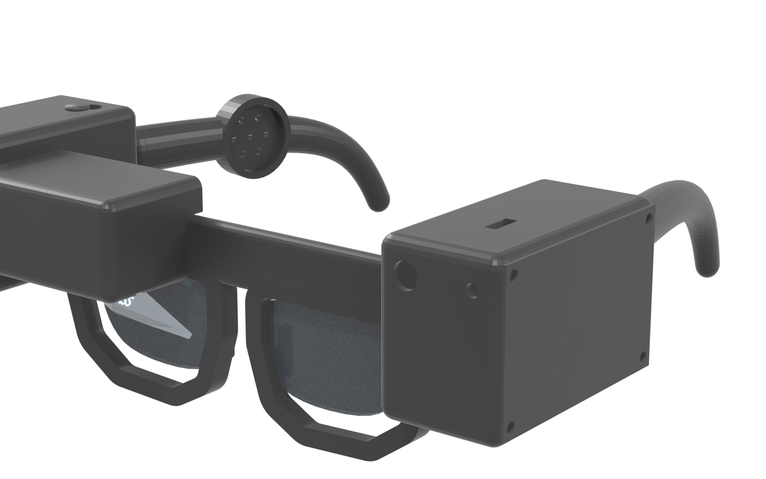
renders/frames/f086.png
