JerzySukiennik/gzowo-glass/renders/frames/f087.png

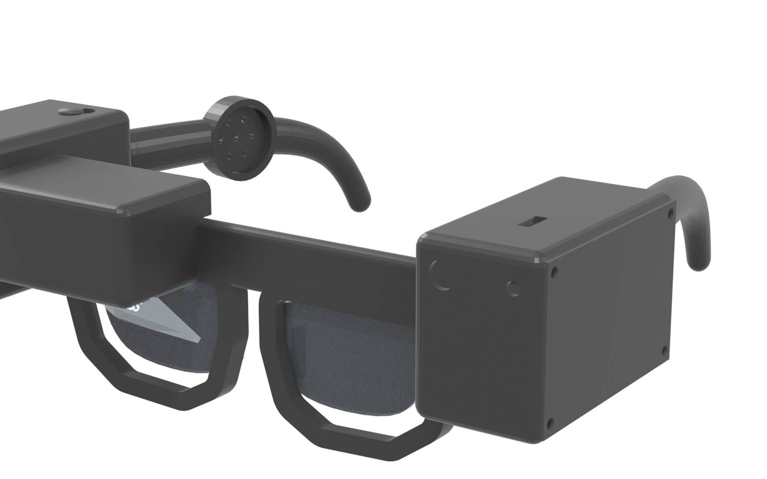
renders/frames/f087.png
