JerzySukiennik/gzowo-glass/renders/frames/f088.png

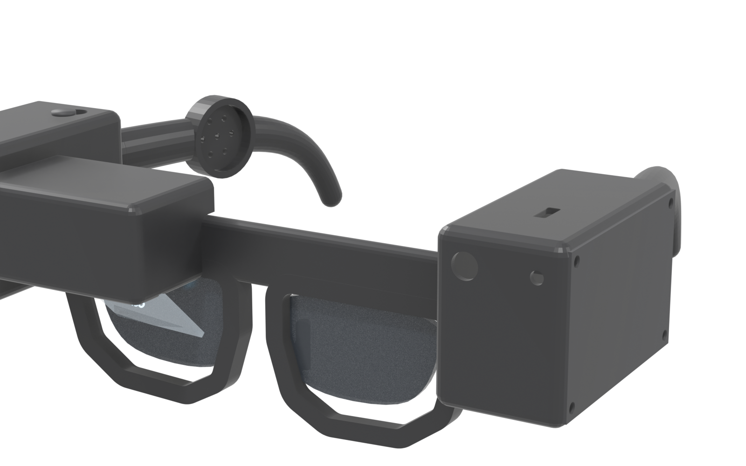
renders/frames/f088.png
