JerzySukiennik/gzowo-glass/renders/frames/f089.png

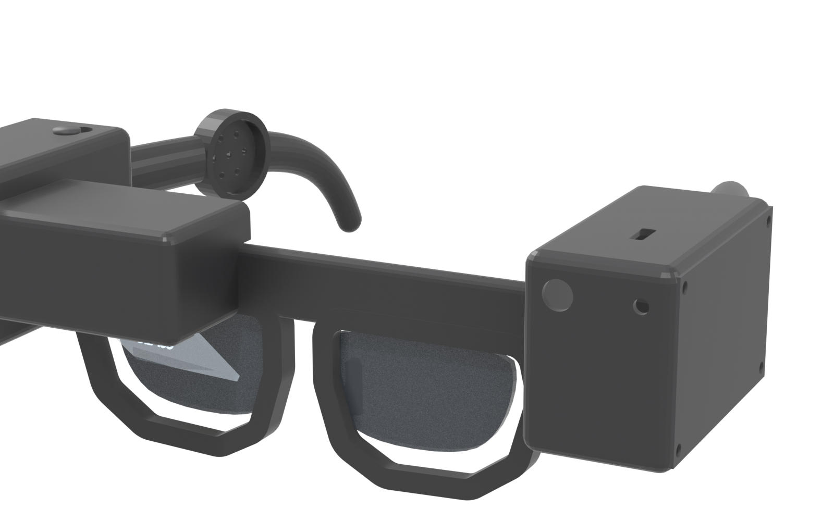
renders/frames/f089.png
