JerzySukiennik/gzowo-glass/renders/frames/f091.png

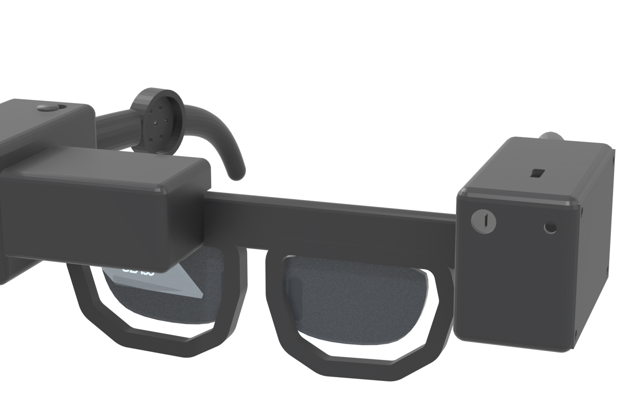
renders/frames/f091.png
