JerzySukiennik/gzowo-glass/renders/frames/f092.png

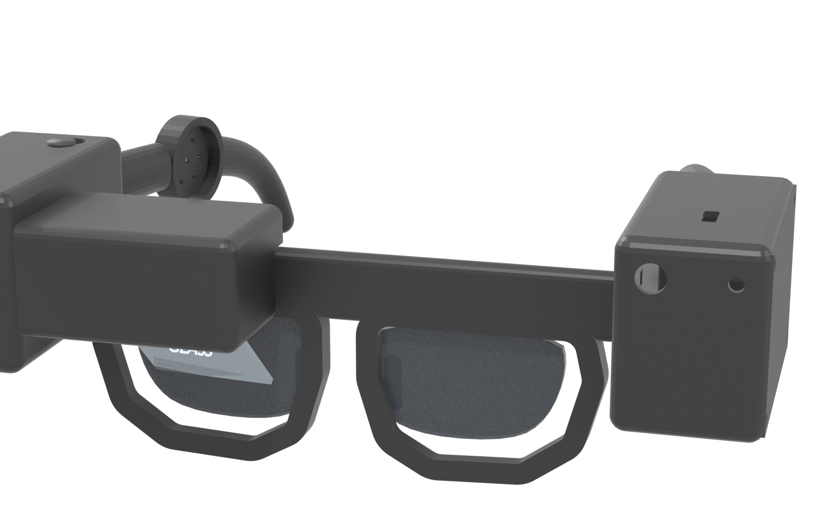
renders/frames/f092.png
