JerzySukiennik/gzowo-glass/renders/frames/f093.png

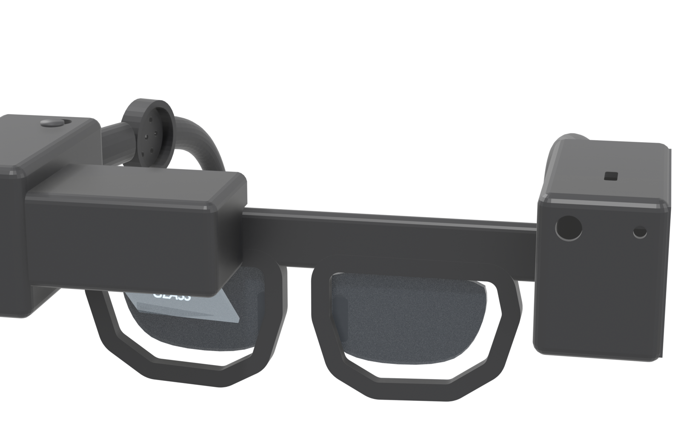
renders/frames/f093.png
