JerzySukiennik/gzowo-glass/renders/frames/f094.png

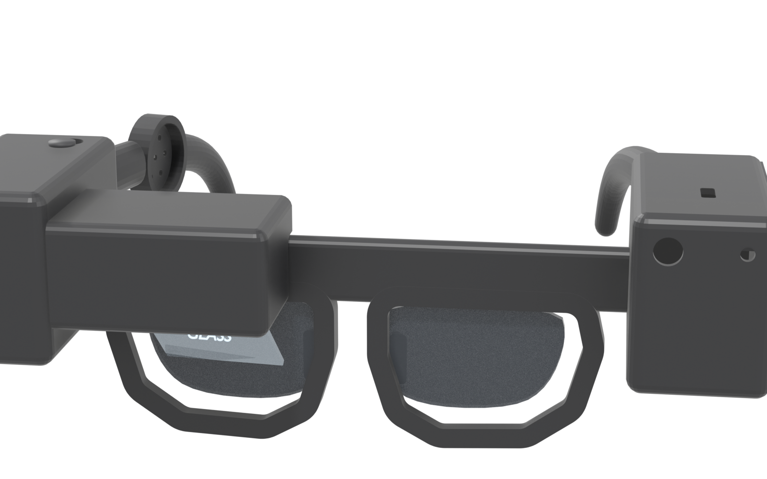
renders/frames/f094.png
