JerzySukiennik/gzowo-glass/renders/glass-beam-path-top.png

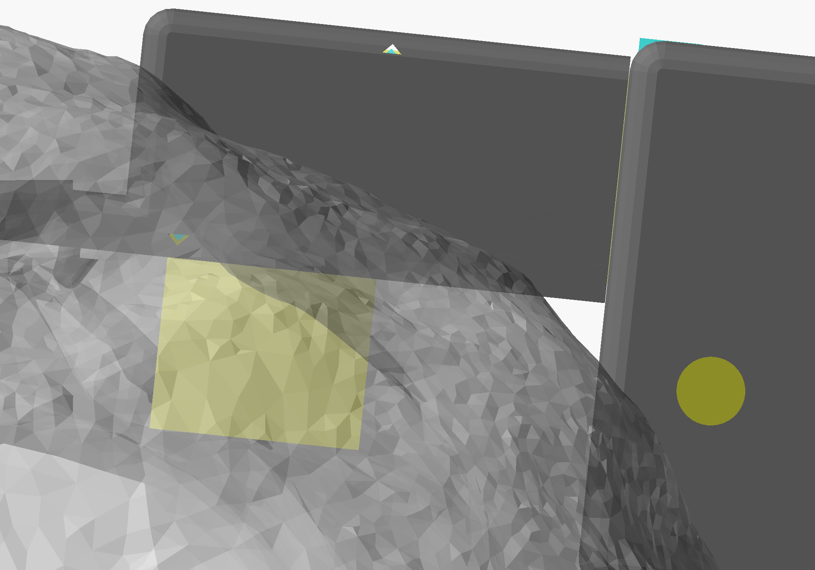
renders/glass-beam-path-top.png
