JerzySukiennik/gzowo-glass/renders/glass-detail-pod.png

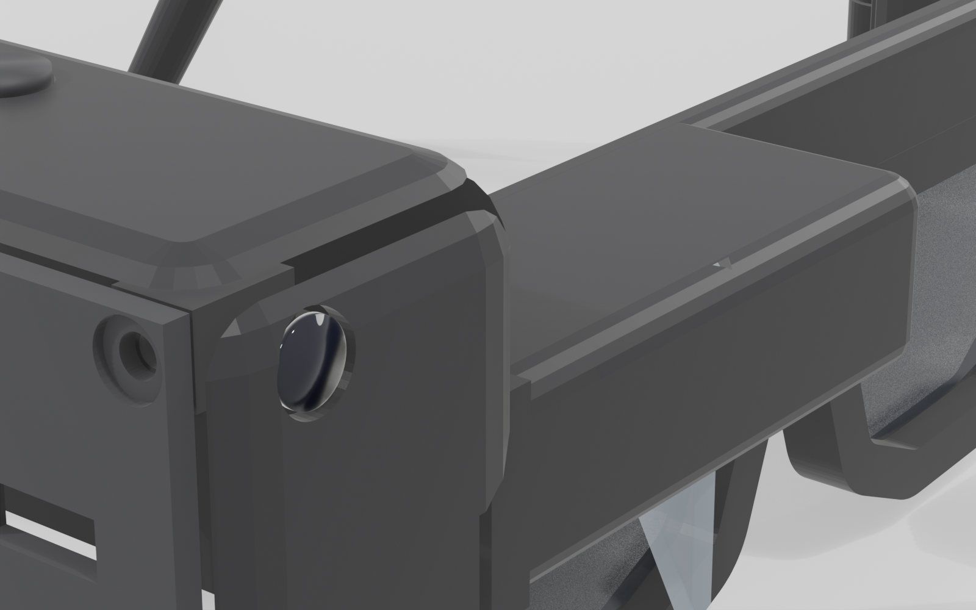
renders/glass-detail-pod.png
