JerzySukiennik/gzowo-glass/renders/glass-head-front34.png

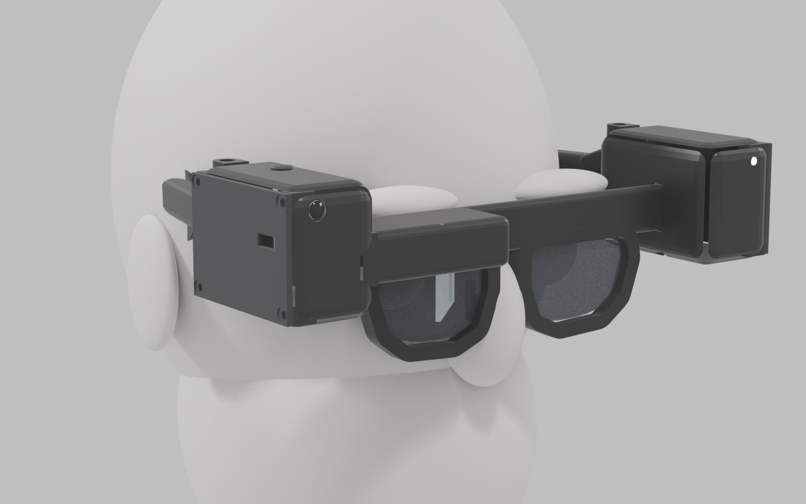
renders/glass-head-front34.png
