JerzySukiennik/gzowo-glass/renders/glass-head-front.png

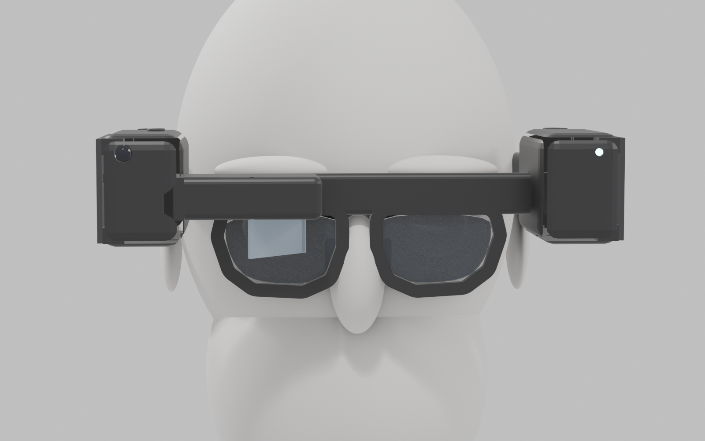
renders/glass-head-front.png
