JerzySukiennik/gzowo-glass/renders/glass-head-side.png

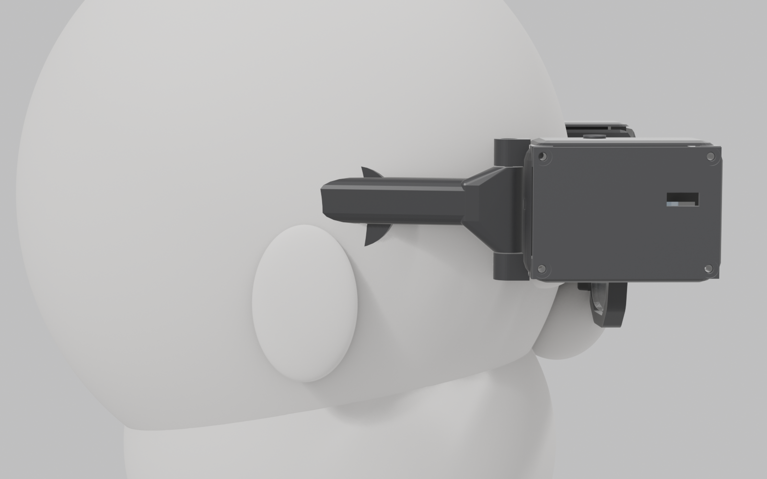
renders/glass-head-side.png
