JerzySukiennik/gzowo-glass/renders/glass-pod-layout-top.png

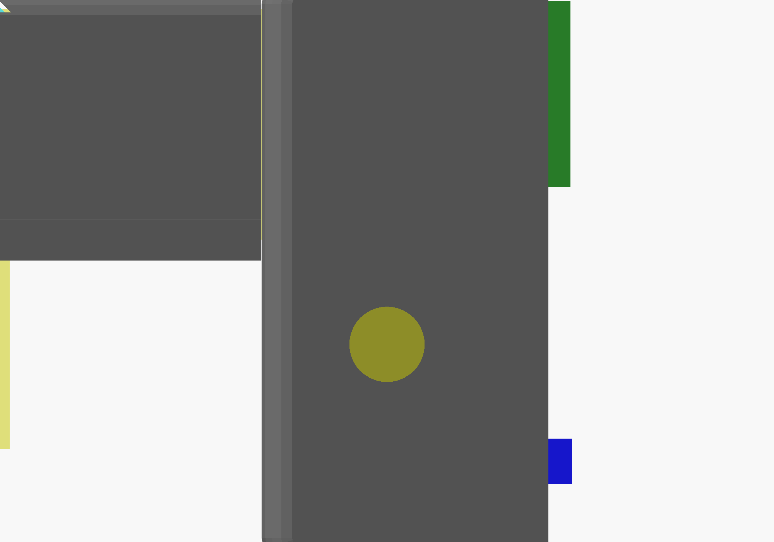
renders/glass-pod-layout-top.png
