JerzySukiennik/gzowo-glass/renders/glass-pod-layout.png

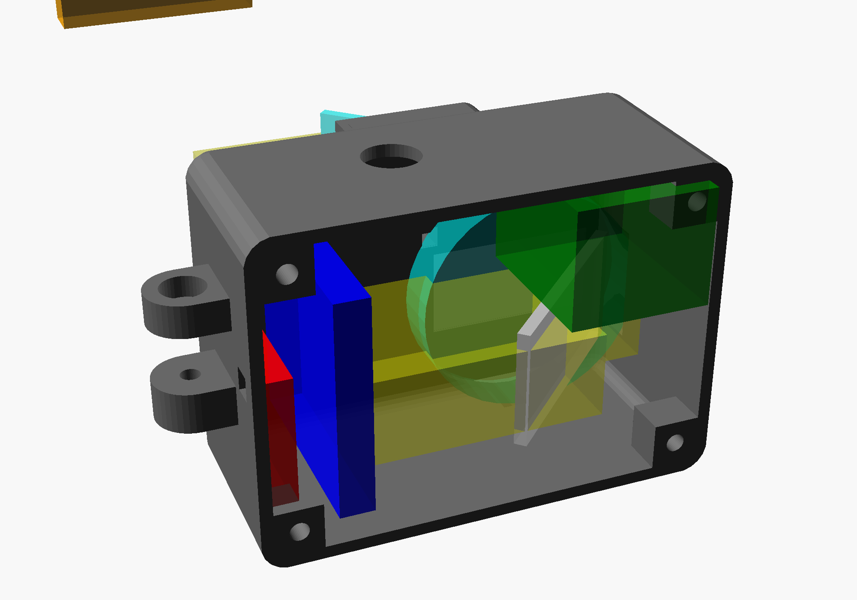
renders/glass-pod-layout.png
