JerzySukiennik/gzowo-glass/renders/glass-product-front34-left.png

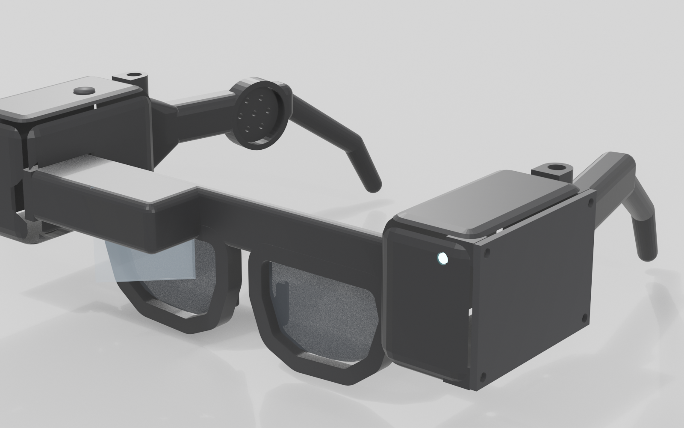
renders/glass-product-front34-left.png
