JerzySukiennik/gzowo-glass/renders/glass-product-front34.png

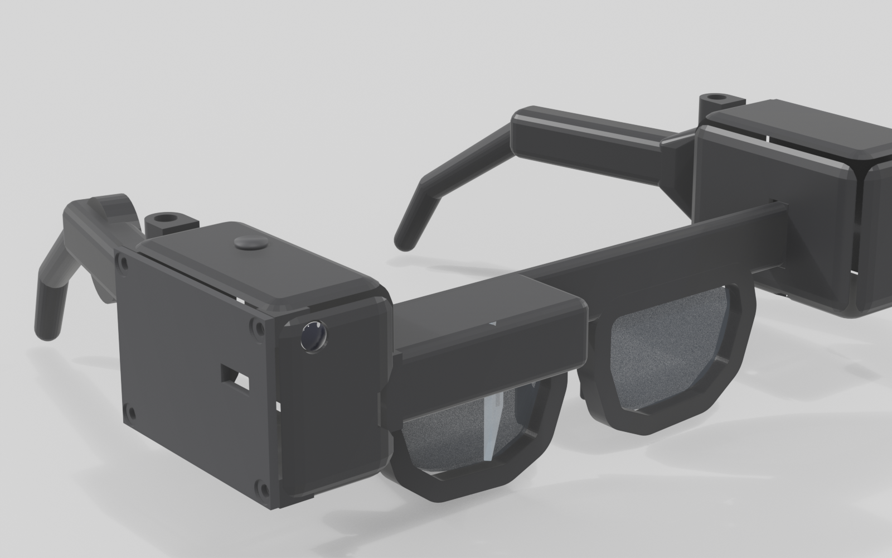
renders/glass-product-front34.png
