JerzySukiennik/gzowo-glass/renders/glass-product-top.png

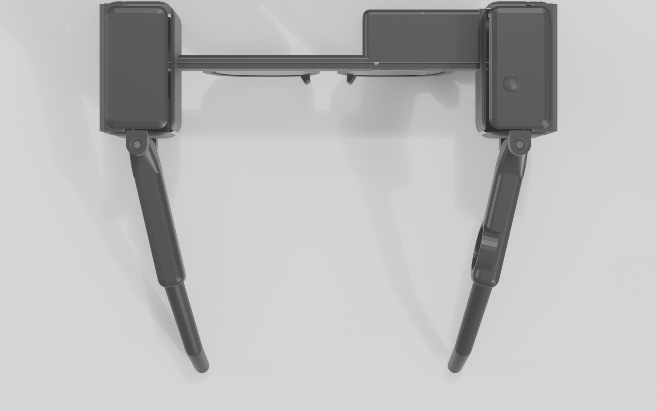
renders/glass-product-top.png
