JerzySukiennik/gzowo-glass/renders/glass-scan-front34.png

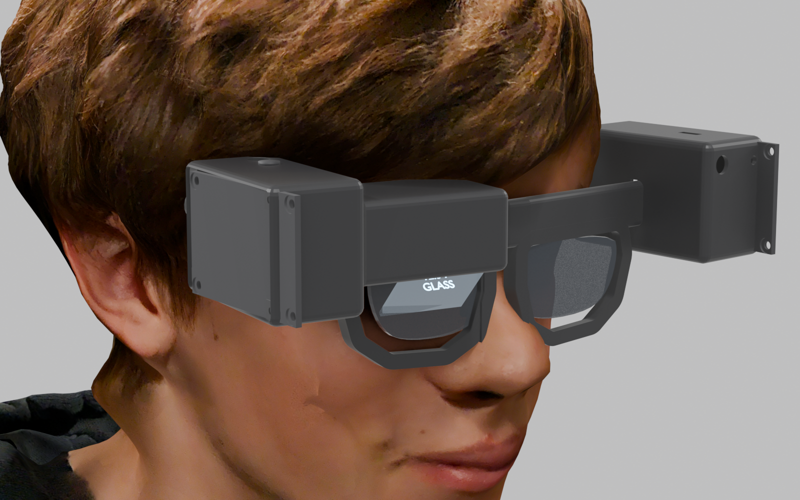
renders/glass-scan-front34.png
