JerzySukiennik/gzowo-glass/renders/glass-scan-front.png

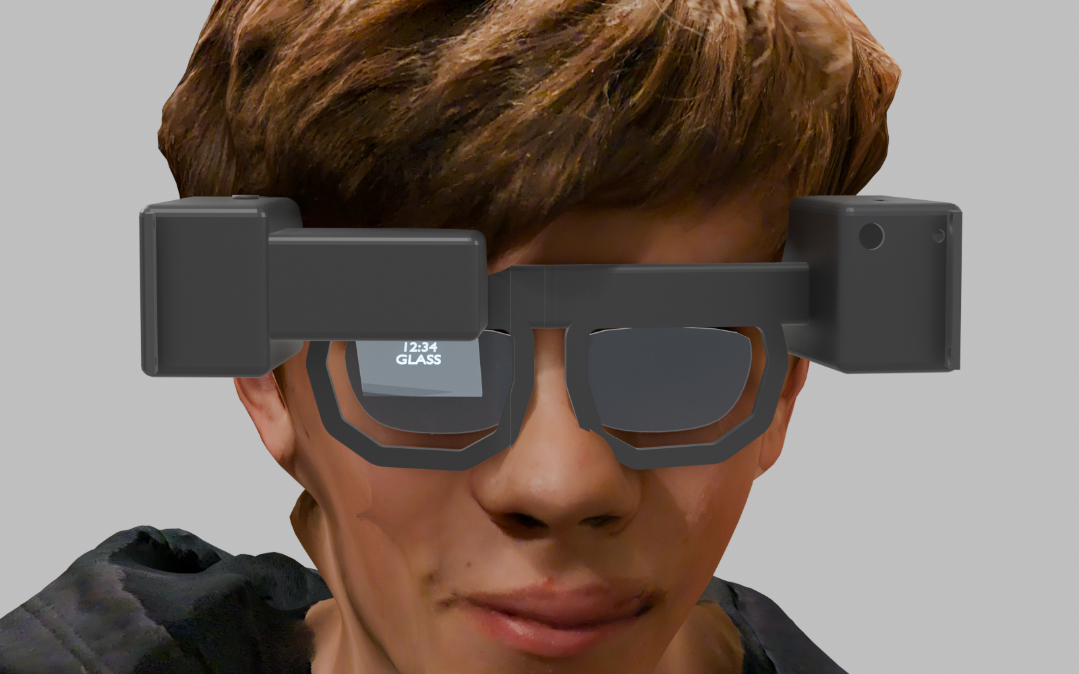
renders/glass-scan-front.png
