JerzySukiennik/gzowo-glass/renders/glass-scan-side-xray.png

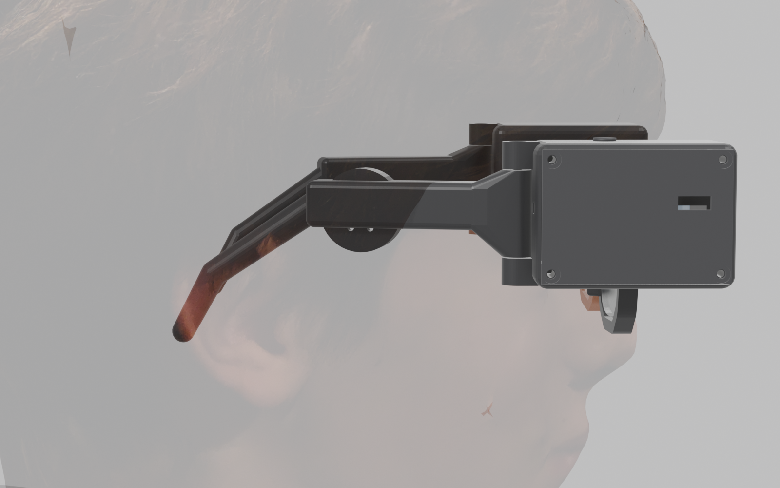
renders/glass-scan-side-xray.png
