JerzySukiennik/gzowo-glass/renders/site-eye.png

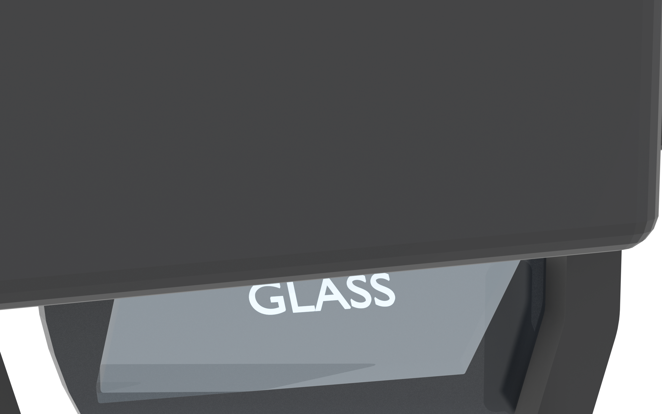
renders/site-eye.png
