JerzySukiennik/gzowo-glass/renders/site-front.png

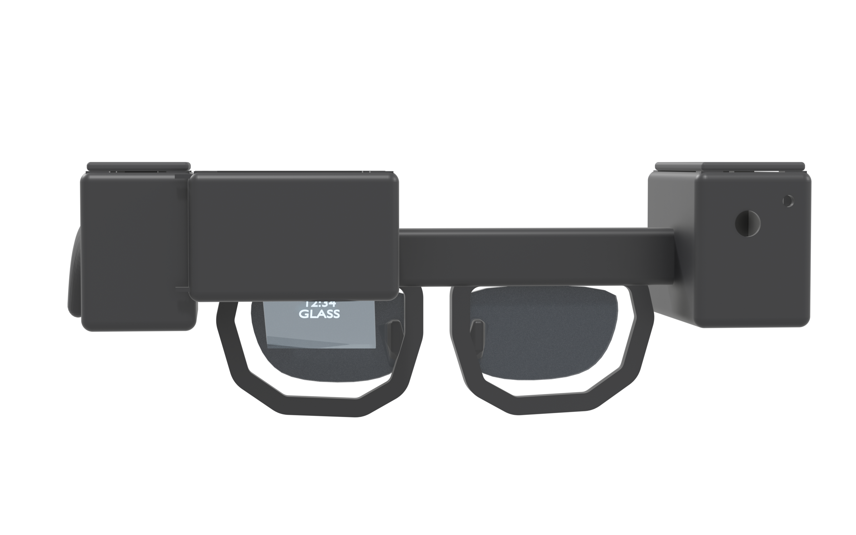
renders/site-front.png
