JerzySukiennik/gzowo-glass/renders/site-hero.png

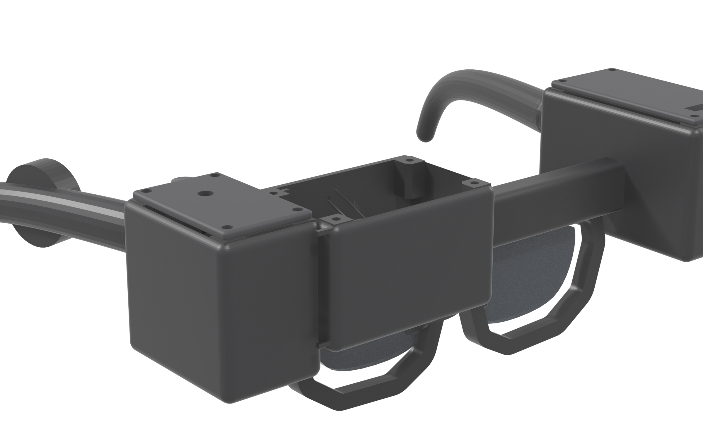
renders/site-hero.png
