JerzySukiennik/gzowo-glass/renders/site-left.png

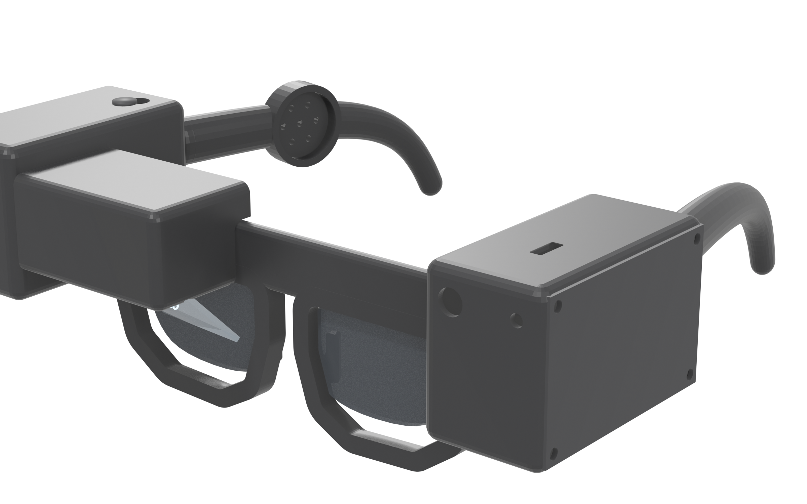
renders/site-left.png
