JerzySukiennik/gzowo-glass/glass-fit-test-v0.2/pegs.stl

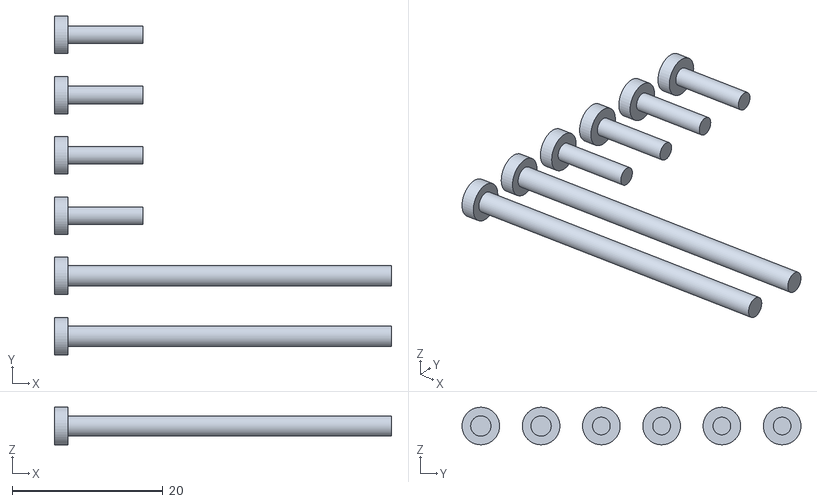
[picture p213: CAD file, 2026-09-11, an earlier design]
glass-fit-test-v0.2/pegs.stl
44.8 x 45.0 x 5.00
