JerzySukiennik/gzowo-glass/glass-fit-test-v0.2/pod_l.stl

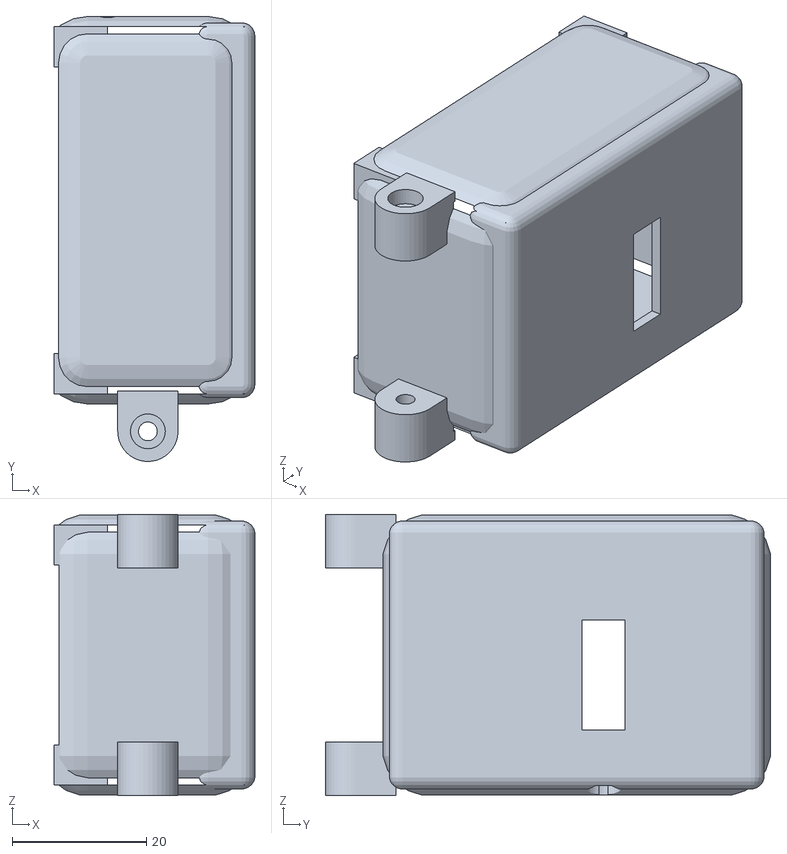
[picture p214: CAD file, 2026-09-11, an earlier design]
glass-fit-test-v0.2/pod_l.stl
30.0 x 66.4 x 42.0
